besser435/Ted/VORON Print Files/Bunged Up Files (Made for v0.1)/Voron-0-0.1/DXF/Tophat/Side_v0.1_x2.DXF

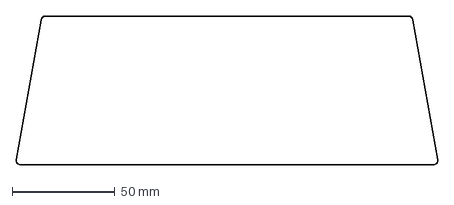
[picture p15: CAD file, 2023-02-20]
VORON Print Files/Bunged Up Files (Made for v0.1)/Voron-0-0.1/DXF/Tophat/Side_v0.1_x2.DXF
205.4 x 72.4 mm
