besser435/Ted/VORON Print Files/Bunged Up Files (Made for v0.1)/Voron-0-0.1/STLs/Panel_Mounting/Door_Latch_x2.STL

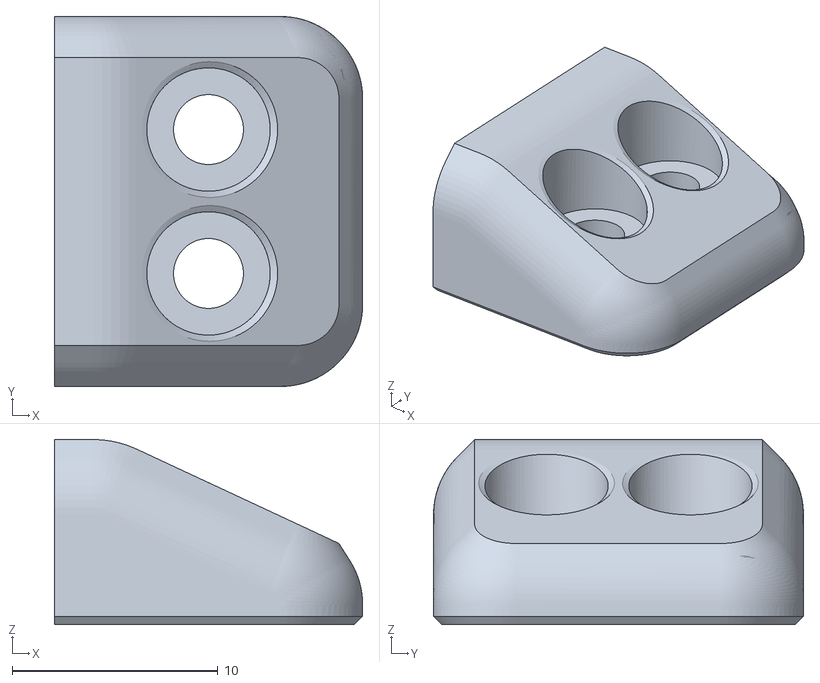
[picture p16: CAD file, 2023-02-20]
VORON Print Files/Bunged Up Files (Made for v0.1)/Voron-0-0.1/STLs/Panel_Mounting/Door_Latch_x2.STL
15.0 x 18.0 x 9.00
