besser435/Ted/VORON Print Files/Bunged Up Files (Made for v0.1)/Voron-0-0.1/STLs/Panel_Mounting/For_2mm_Panels/2mm_Bottom_Corner_Side_mirror_x1.STL

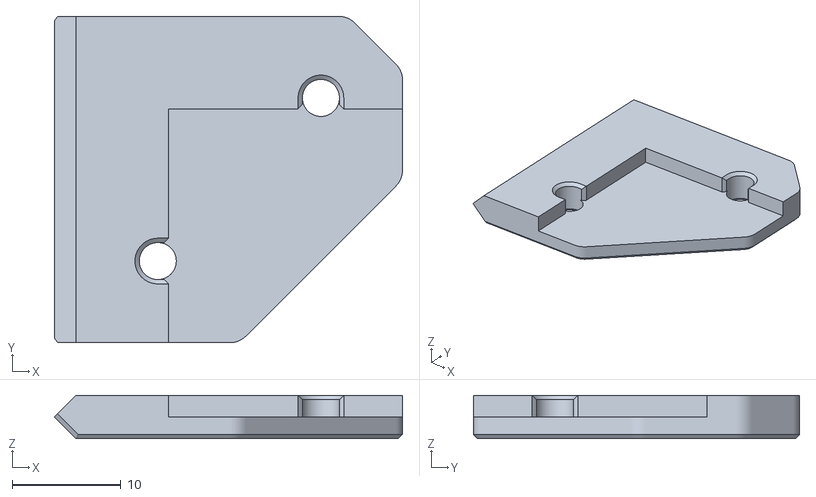
[picture p18: CAD file, 2023-02-20]
VORON Print Files/Bunged Up Files (Made for v0.1)/Voron-0-0.1/STLs/Panel_Mounting/For_2mm_Panels/2mm_Bottom_Corner_Side_mirror_x1.STL
32.0 x 30.0 x 4.00
