besser435/Ted/VORON Print Files/Bunged Up Files (Made for v0.1)/Voron-0-0.1/STLs/Toolheads/Bowden/[a]_Endstop_Strike_Block_x1.STL

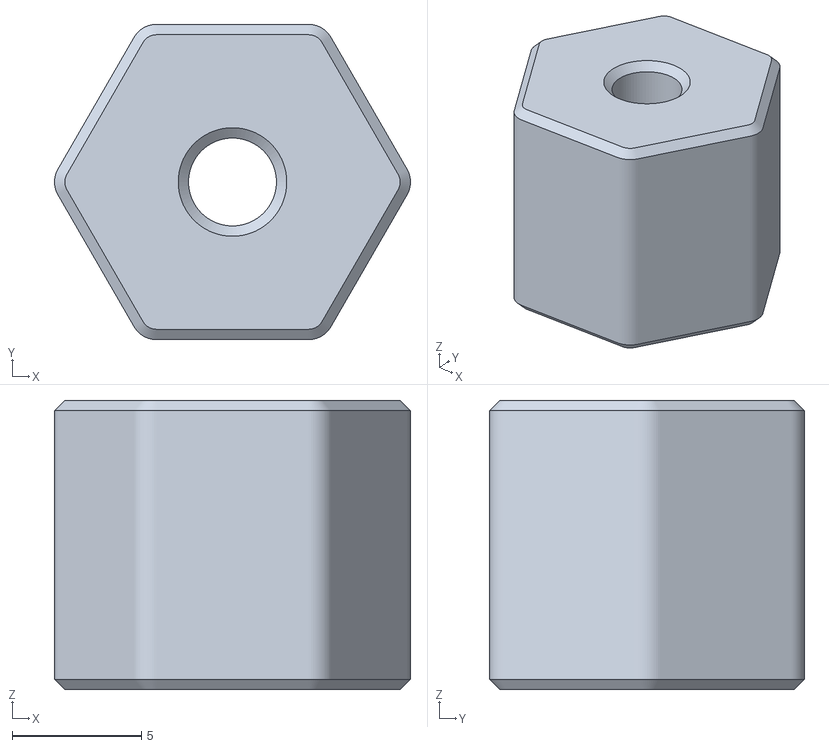
[picture p20: CAD file, 2023-02-20]
VORON Print Files/Bunged Up Files (Made for v0.1)/Voron-0-0.1/STLs/Toolheads/Bowden/[a]_Endstop_Strike_Block_x1.STL
13.8 x 12.2 x 11.2
