besser435/Ted/VORON Print Files/Bunged Up Files (Made for v0.1)/Voron-0-0.1/STLs/Toolheads/Bowden/Mosquito_Toolhead/Toolhead_Left_Mosquito_x1.STL

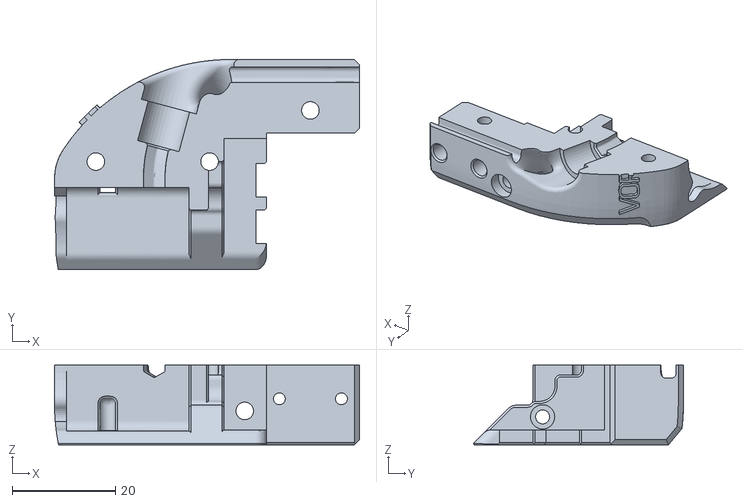
[picture p22: CAD file, 2023-02-20]
VORON Print Files/Bunged Up Files (Made for v0.1)/Voron-0-0.1/STLs/Toolheads/Bowden/Mosquito_Toolhead/Toolhead_Left_Mosquito_x1.STL
59.0 x 40.6 x 15.4
