besser435/Ted/VORON Print Files/Bunged Up Files (Made for v0.1)/Voron-0-0.1/STLs/Toolheads/Mini_Afterburner/Dragonfly_BMO_Toolhead_DD/[a]_Cowling_BMO_x1.STL

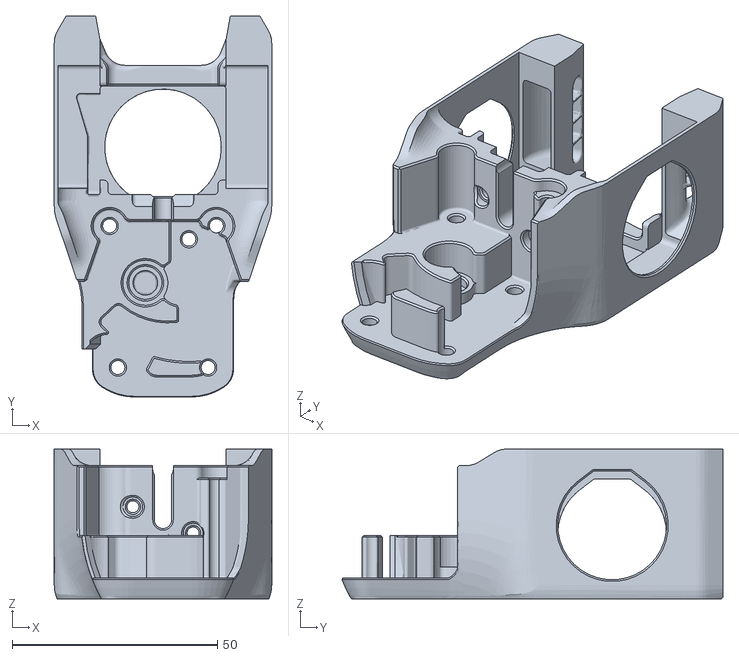
[picture p24: CAD file, 2023-02-20]
VORON Print Files/Bunged Up Files (Made for v0.1)/Voron-0-0.1/STLs/Toolheads/Mini_Afterburner/Dragonfly_BMO_Toolhead_DD/[a]_Cowling_BMO_x1.STL
53.0 x 92.8 x 36.5
