besser435/Ted/VORON Print Files/Bunged Up Files (Made for v0.1)/Voron-0-0.1/STLs/Toolheads/Mini_Afterburner/Motor_Frame_x1.stl

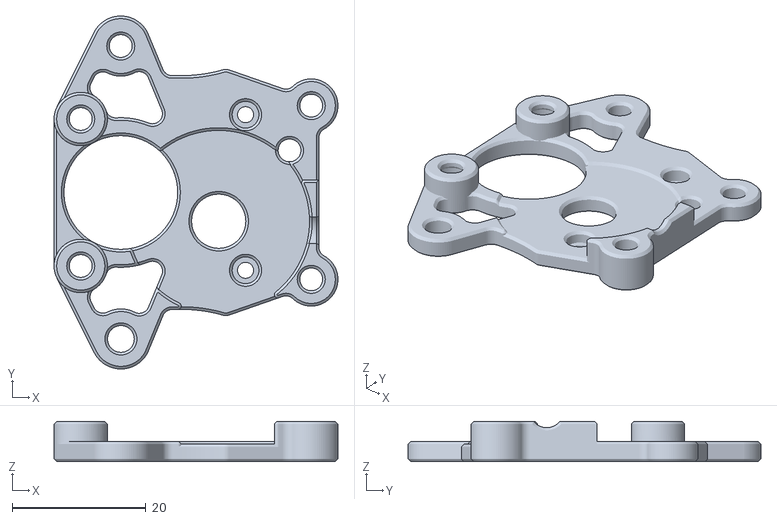
[picture p25: CAD file, 2023-02-20]
VORON Print Files/Bunged Up Files (Made for v0.1)/Voron-0-0.1/STLs/Toolheads/Mini_Afterburner/Motor_Frame_x1.stl
42.5 x 52.8 x 6.00
