besser435/Ted/VORON Print Files/Bunged Up Files (Made for v0.1)/Voron-0-0.1/STLs/Tophat/Left_and_Right_Midclip_x2.STL

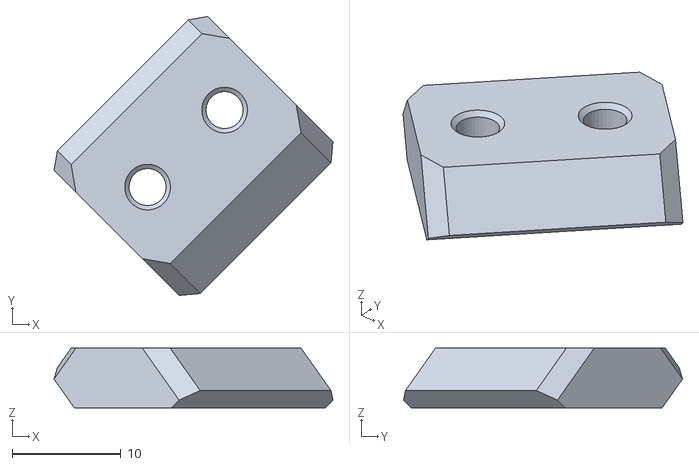
[picture p26: CAD file, 2023-02-20]
VORON Print Files/Bunged Up Files (Made for v0.1)/Voron-0-0.1/STLs/Tophat/Left_and_Right_Midclip_x2.STL
25.6 x 25.6 x 5.50
