besser435/Ted/VORON Print Files/Enclosure/Enclosure.3mf

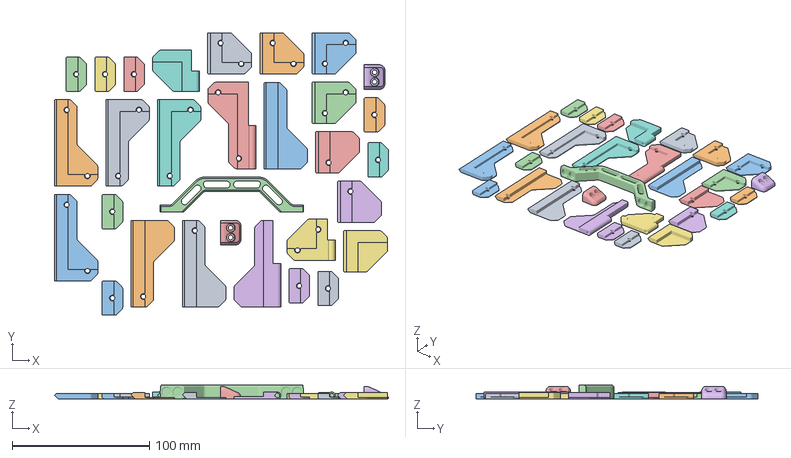
[picture p27: CAD file, 2023-02-20]
VORON Print Files/Enclosure/Enclosure.3mf
243.1 x 205.6 x 10.0 mm
2point5mm_Top_Corner_Rear_x1.STL
2point5mm_Top_Corner_Rear_mirror_x1.stl
2point5mm_Top_Corner_Front_x1.STL
2point5mm_Middle_Clip_x9.STL
2point5mm_Hinge_Top_B_x1.STL
2point5mm_Hinge_Top_A_x1.STL
2point5mm_Hinge_Bottom_B_x1.STL
2point5mm_Hinge_Bottom_A_x1.STL
2point5mm_Bottom_Corner_Side_x2.STL
2point5mm_Bottom_Corner_Side_mirror_x2.stl
2point5mm_Bottom_Corner_Rear_x1.STL
2point5mm_Bottom_Corner_Rear_mirror_x1.stl
2point5mm_Bottom_Corner_Front_x1.STL
2point5mm_Top_Corner_Side_x2.STL
2point5mm_Top_Corner_Side_mirror_x2.stl
Door_Handle_x1.STL
Door_Latch_x2.STL
