besser435/Ted/VORON Print Files/Enclosure/For_2.5mm_Panels/2point5mm_Top_Corner_Side_x2.STL

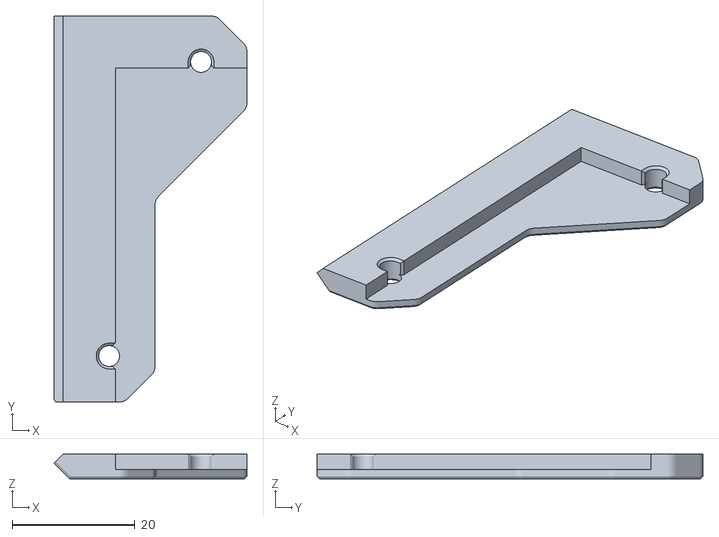
[picture p28: CAD file, 2023-02-20]
VORON Print Files/Enclosure/For_2.5mm_Panels/2point5mm_Top_Corner_Side_x2.STL
31.5 x 63.0 x 4.00
