besser435/Ted/VORON Print Files/Enclosure/For_2mm_Panels/2mm_Bottom_Corner_Rear_mirror_x1.STL

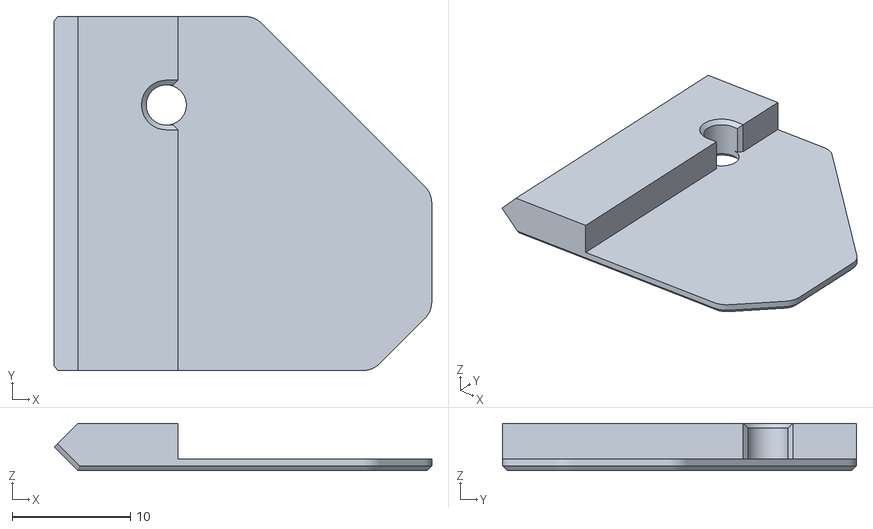
[picture p30: CAD file, 2023-02-20]
VORON Print Files/Enclosure/For_2mm_Panels/2mm_Bottom_Corner_Rear_mirror_x1.STL
32.0 x 30.0 x 4.00
