besser435/Ted/VORON Print Files/Enclosure/For_3mm_Panels/3mm_Top_Corner_Rear_x1.stl

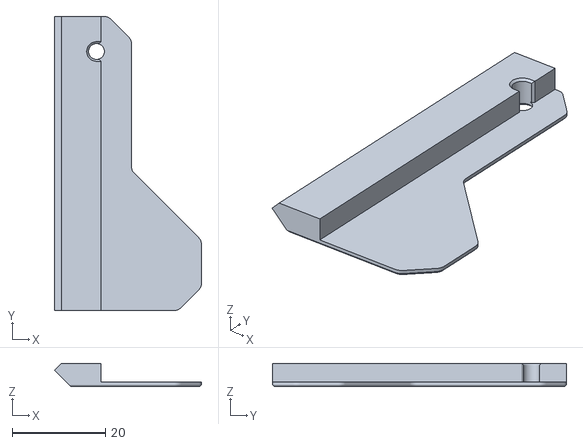
[picture p31: CAD file, 2023-02-20]
VORON Print Files/Enclosure/For_3mm_Panels/3mm_Top_Corner_Rear_x1.stl
31.5 x 63.0 x 5.00
