besser435/Ted/VORON Print Files/Main Parts/Batch 1 Main Parts/Accent Batch 1 Main Parts/[a]_Z_Endstop_Mount_x1.STL

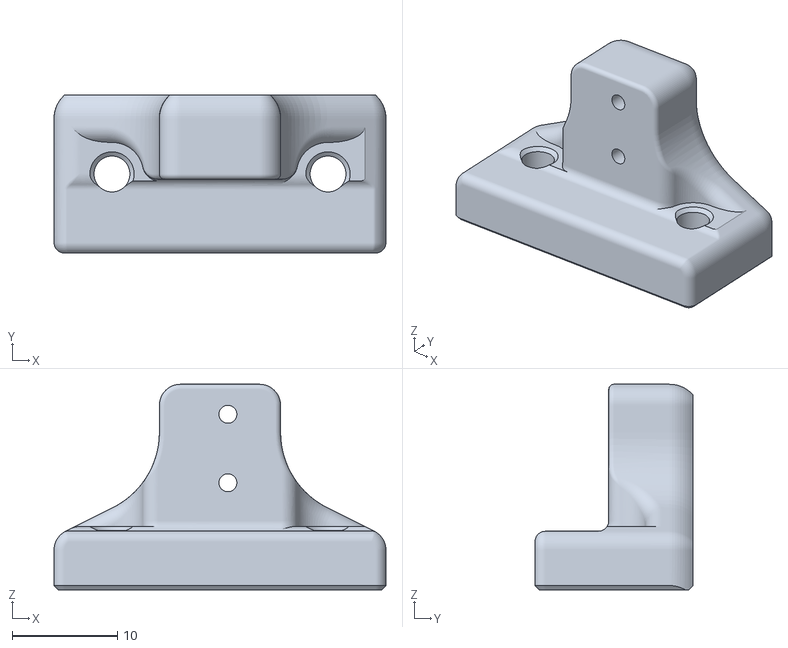
[picture p32: CAD file, 2023-02-20]
VORON Print Files/Main Parts/Batch 1 Main Parts/Accent Batch 1 Main Parts/[a]_Z_Endstop_Mount_x1.STL
31.5 x 15.0 x 19.5
