besser435/Ted/VORON Print Files/Main Parts/Batch 2 Main Parts/RPi_Frame_x1.stl

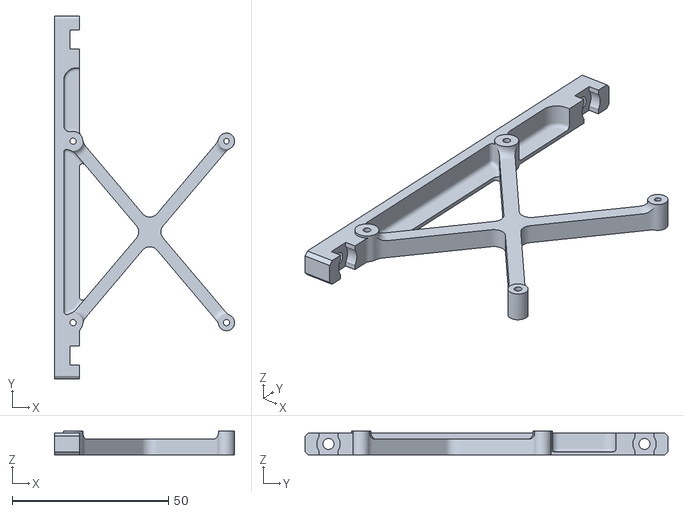
[picture p33: CAD file, 2023-02-20]
VORON Print Files/Main Parts/Batch 2 Main Parts/RPi_Frame_x1.stl
57.6 x 116.0 x 7.60
