besser435/Ted/VORON Print Files/Main Parts/Multiples Main Parts/One Part Skirts/V0_skirts_onepart.3mf

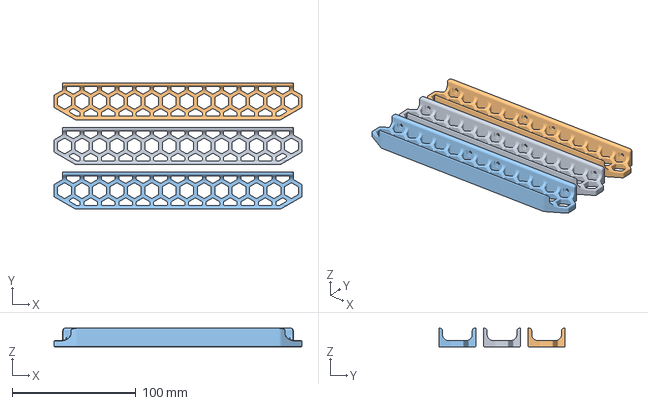
[picture p34: CAD file, 2023-02-20]
VORON Print Files/Main Parts/Multiples Main Parts/One Part Skirts/V0_skirts_onepart.3mf
200.0 x 102.0 x 15.0 mm
