besser435/Ted/VORON Print Files/Main Parts/Multiples Main Parts/Skirt_mirror_x3.STL

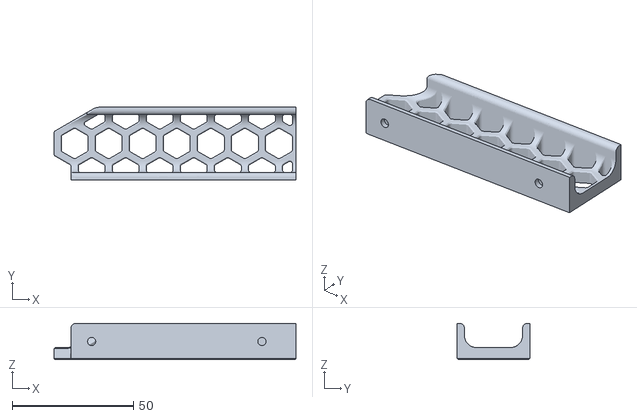
[picture p35: CAD file, 2023-02-20]
VORON Print Files/Main Parts/Multiples Main Parts/Skirt_mirror_x3.STL
100.0 x 30.0 x 15.0
