besser435/Ted/VORON Print Files/Main Parts/Nema17 Extruder latch and latch movey thing.3mf

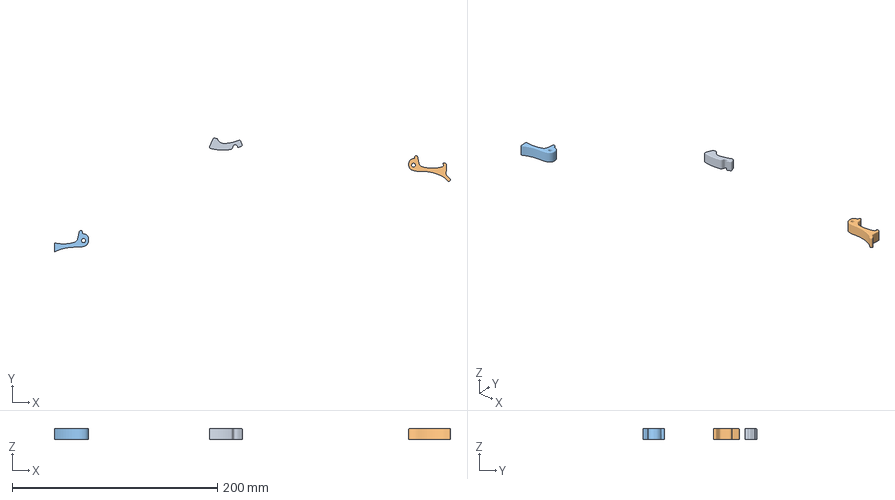
[picture p36: CAD file, 2023-02-20]
VORON Print Files/Main Parts/Nema17 Extruder latch and latch movey thing.3mf
385.8 x 110.9 x 11.1 mm
[a]_Latch_Shuttle_x1.STL
[a]_Latch_x1.STL
V0 Extruder Latch.stl
