besser435/Ted/VORON Print Files/New Cooling/Fan Shrouds, Embiggend Holes.3mf

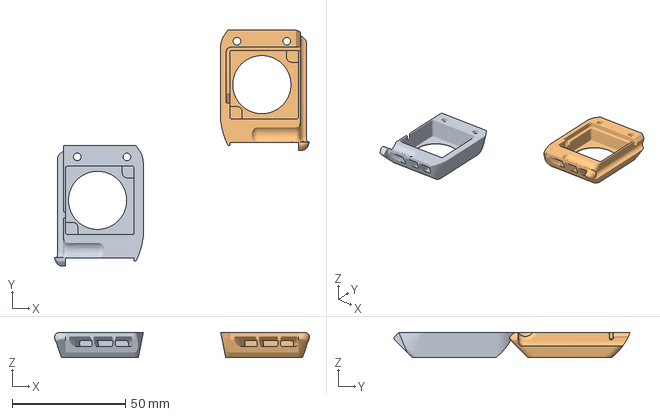
[picture p37: CAD file, 2023-02-20]
VORON Print Files/New Cooling/Fan Shrouds, Embiggend Holes.3mf
112.7 x 104.5 x 11.2 mm
VORON Part Cooling (6).stl_1
VORON Part Cooling (6).stl_2
