besser435/Ted/VORON Print Files/Toolhead/Accent Toolhead/[a]_Toolhead_Blower_Duct_Left_TV6_x1.STL

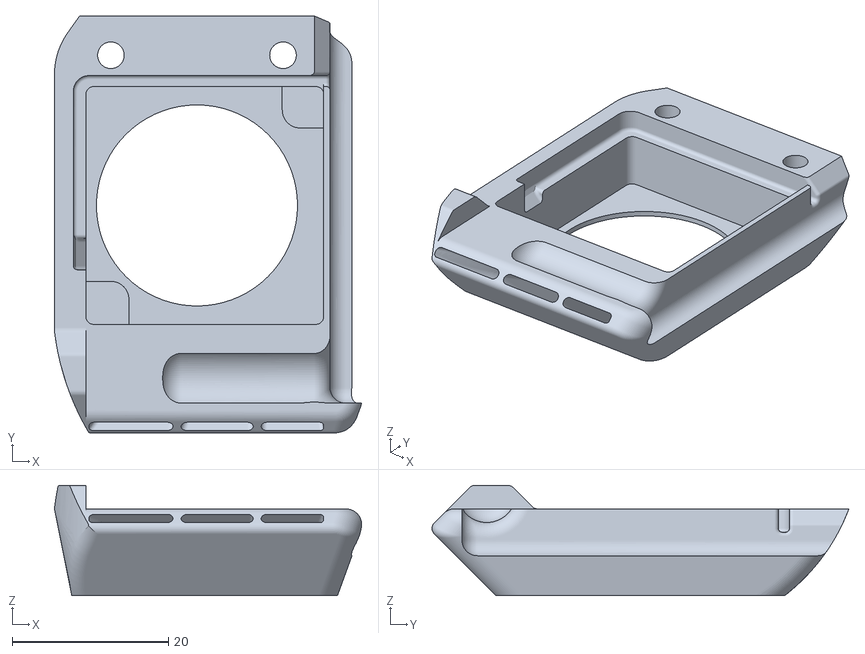
[picture p38: CAD file, 2023-02-20]
VORON Print Files/Toolhead/Accent Toolhead/[a]_Toolhead_Blower_Duct_Left_TV6_x1.STL
39.3 x 53.3 x 14.1
