besser435/Ted/VORON Print Files/Toolhead/Toolhead_Left_Threaded_V6_x1.STL

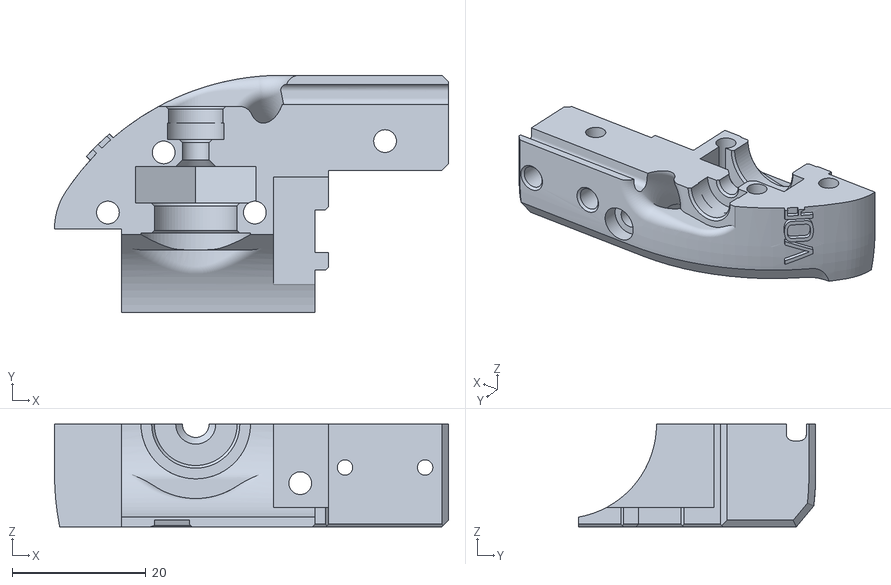
[picture p39: CAD file, 2023-02-20]
VORON Print Files/Toolhead/Toolhead_Left_Threaded_V6_x1.STL
59.0 x 35.6 x 15.4
