besser435/Ted/VORON Print Files/Tophat/TopHat_Left_x2.stl

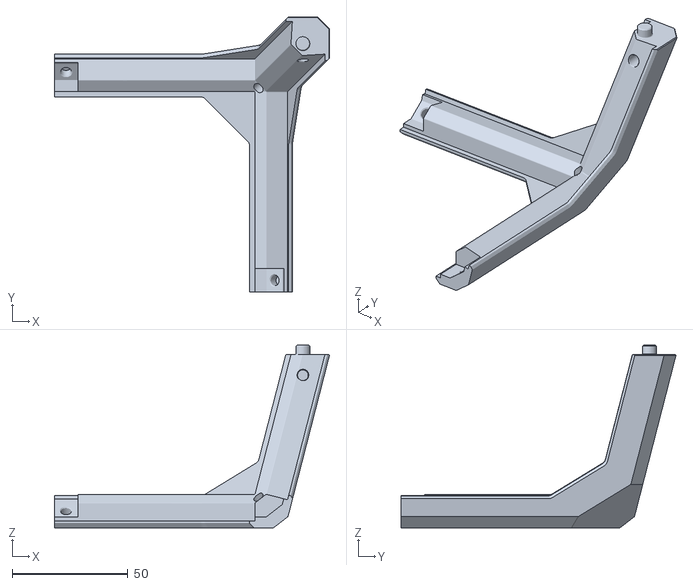
[picture p40: CAD file, 2023-02-20]
VORON Print Files/Tophat/TopHat_Left_x2.stl
119.0 x 119.0 x 79.0
