besser435/Ted/VORON Print Files/Tophat/TopHat_Panel_Mounting/For_2mm_Panels/2mm_TH_Mid_Clip_x4.STL

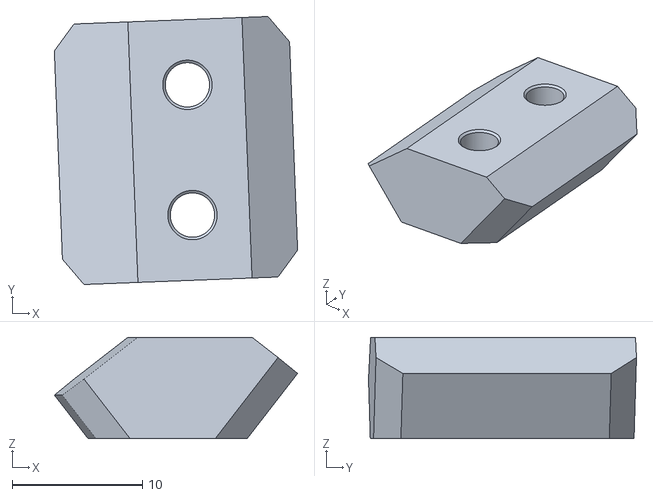
[picture p42: CAD file, 2023-02-20]
VORON Print Files/Tophat/TopHat_Panel_Mounting/For_2mm_Panels/2mm_TH_Mid_Clip_x4.STL
18.7 x 20.6 x 7.78
