besser435/Ted/VORON Print Files/Tophat/TopHat_Panel_Mounting/For_3mm_Panels/3mm_TH_Top_Corner_Clips_x4.STL

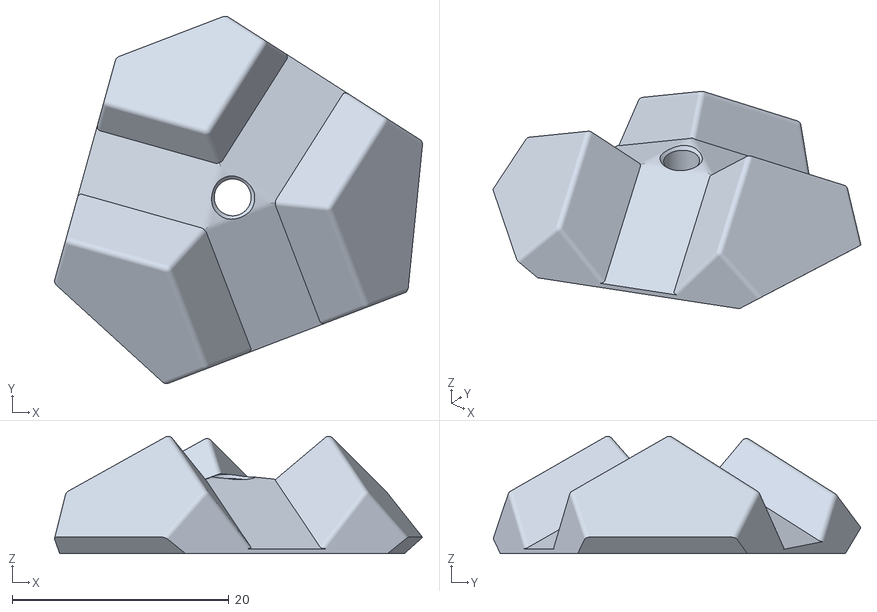
[picture p43: CAD file, 2023-02-20]
VORON Print Files/Tophat/TopHat_Panel_Mounting/For_3mm_Panels/3mm_TH_Top_Corner_Clips_x4.STL
34.0 x 33.9 x 10.8
