besser435/Ted/VORON Print Files/VORON-0 Everything/DXFs/Deck_Panel_Rear_V0.DXF

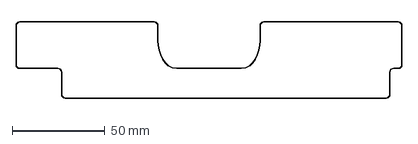
[picture p44: CAD file, 2023-02-20]
VORON Print Files/VORON-0 Everything/DXFs/Deck_Panel_Rear_V0.DXF
208.0 x 41.0 mm
