besser435/Ted/VORON Print Files/VORON-0 Everything/STLs/[a]_Foot_Front_x2.stl

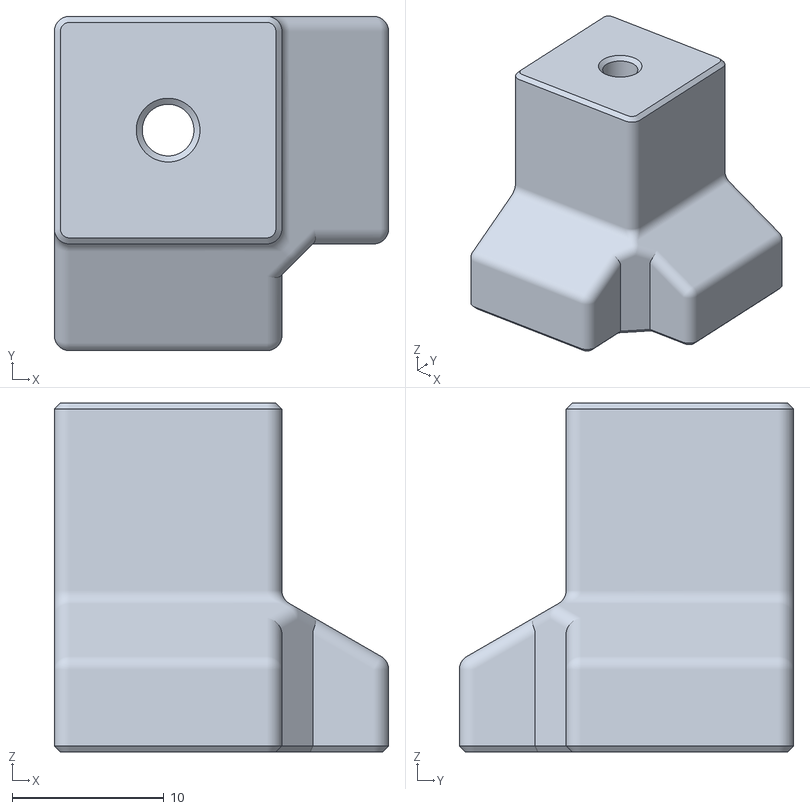
[picture p45: CAD file, 2023-02-20]
VORON Print Files/VORON-0 Everything/STLs/[a]_Foot_Front_x2.stl
22.0 x 22.0 x 23.0
