besser435/Ted/VORON Print Files/VORON-0 Everything/STLs/Mosquito_Toolhead/Toolhead_Right_Mosquito_x1.STL

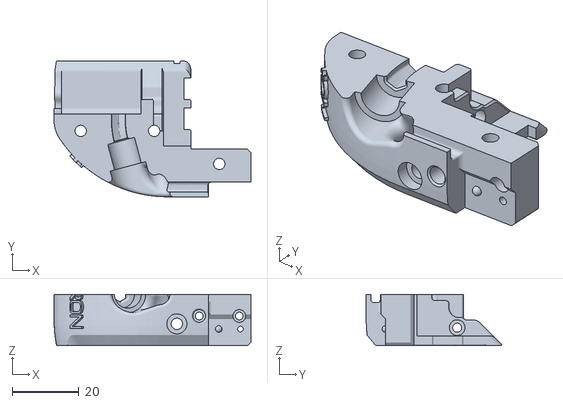
[picture p46: CAD file, 2023-02-20]
VORON Print Files/VORON-0 Everything/STLs/Mosquito_Toolhead/Toolhead_Right_Mosquito_x1.STL
59.0 x 40.6 x 15.4
