besser435/Ted/VORON Print Files/VORON-0 Everything/STLs/V0_TopHat/TopHat_Panel_Mounting/For_2.5mm_Panels/2point5mm_TH_Mid_Clip_x4.STL

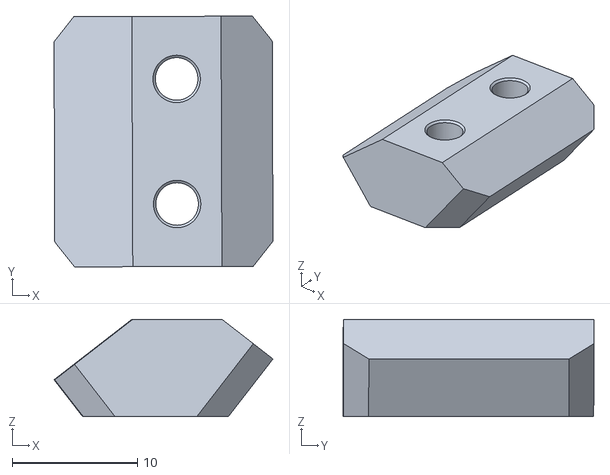
[picture p47: CAD file, 2023-02-20]
VORON Print Files/VORON-0 Everything/STLs/V0_TopHat/TopHat_Panel_Mounting/For_2.5mm_Panels/2point5mm_TH_Mid_Clip_x4.STL
17.5 x 20.1 x 7.78
