besser435/Ted/VORON Print Files/VORON-0 Everything/STLs/V0_TopHat/TopHat_Panel_Mounting/For_2mm_Panels/2mm_TH_Top_Corner_Clips_x4.STL

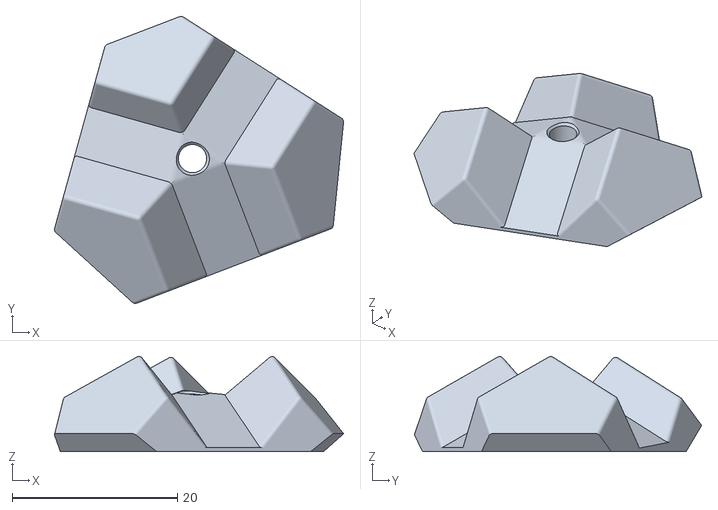
[picture p48: CAD file, 2023-02-20]
VORON Print Files/VORON-0 Everything/STLs/V0_TopHat/TopHat_Panel_Mounting/For_2mm_Panels/2mm_TH_Top_Corner_Clips_x4.STL
34.9 x 34.7 x 11.5
