besser435/Ted/VORON Print Files/VORON-0 Everything/STLs/V0_TopHat/Unibody_Tophat/Unibody_Tophat_x1.STL

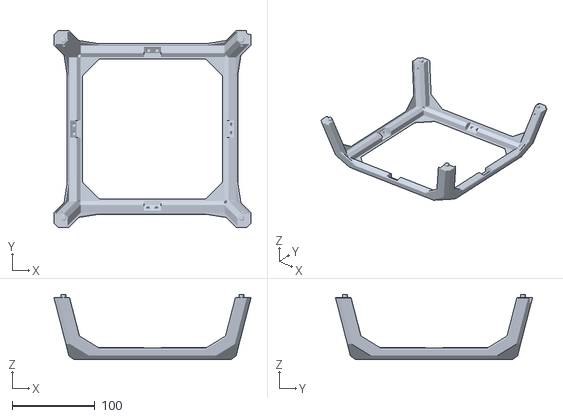
[picture p49: CAD file, 2023-02-20]
VORON Print Files/VORON-0 Everything/STLs/V0_TopHat/Unibody_Tophat/Unibody_Tophat_x1.STL
238.1 x 238.1 x 79.0
