besser435/Ted/VORON Print Files/Bunged Up Files (Made for v0.1)/Enclosure (Contains Multiples)/Lower_Corner_1_and_3_Clip_x2.stl

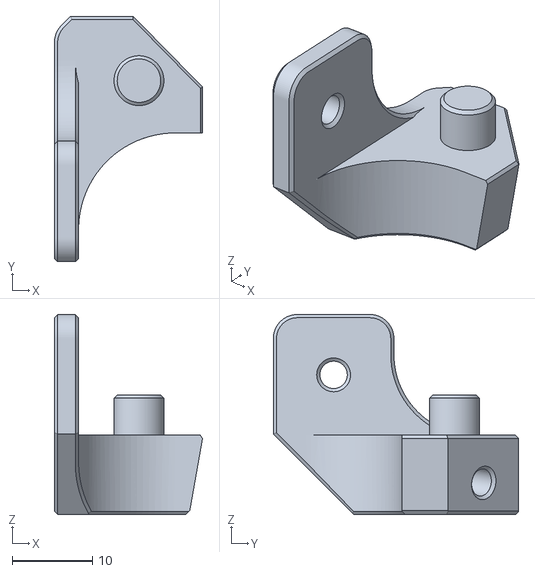
[picture p50: CAD file, 2023-02-20]
VORON Print Files/Bunged Up Files (Made for v0.1)/Enclosure (Contains Multiples)/Lower_Corner_1_and_3_Clip_x2.stl
18.4 x 30.5 x 24.8
