besser435/Ted/VORON Print Files/Bunged Up Files (Made for v0.1)/Mulitples of parts/Skirt_x3.STL

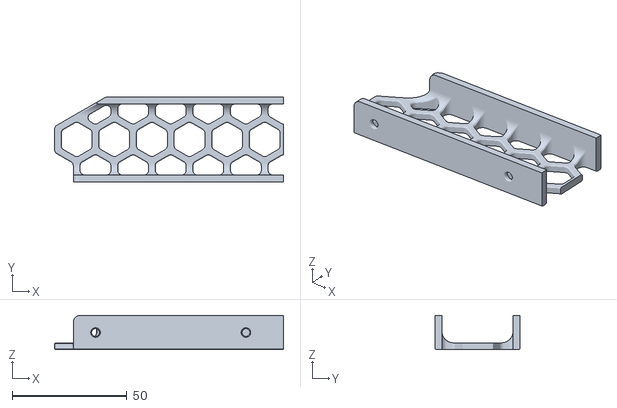
[picture p51: CAD file, 2023-02-20]
VORON Print Files/Bunged Up Files (Made for v0.1)/Mulitples of parts/Skirt_x3.STL
100.0 x 37.0 x 15.0
