besser435/Ted/VORON Print Files/Bunged Up Files (Made for v0.1)/Regular Parts/Batch 1/Accent/A_Drive_Frame_Lower_x1.stl

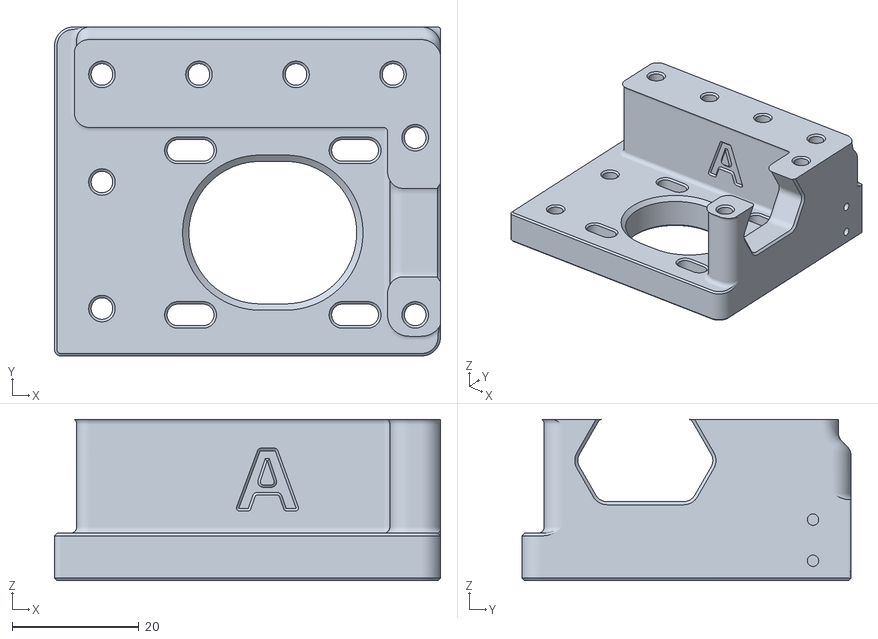
[picture p52: CAD file, 2023-02-20]
VORON Print Files/Bunged Up Files (Made for v0.1)/Regular Parts/Batch 1/Accent/A_Drive_Frame_Lower_x1.stl
61.0 x 52.0 x 25.5
