besser435/Ted/VORON Print Files/Bunged Up Files (Made for v0.1)/Regular Parts/Batch 2 (B)/PSU_Cover_x1.STL

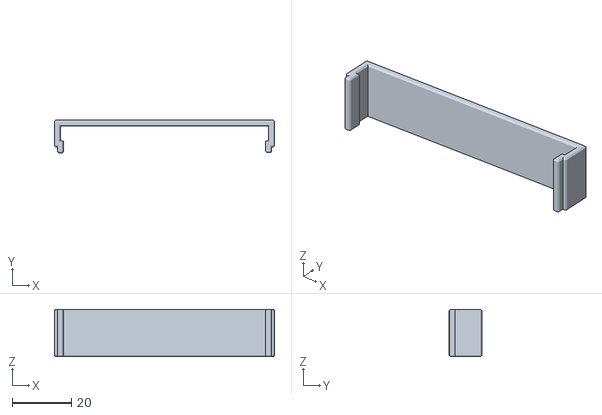
[picture p54: CAD file, 2023-02-20]
VORON Print Files/Bunged Up Files (Made for v0.1)/Regular Parts/Batch 2 (B)/PSU_Cover_x1.STL
74.2 x 11.0 x 16.0
