besser435/Ted/VORON Print Files/Bunged Up Files (Made for v0.1)/Voron-0-0.1/DXF/Rear_Panel_x1.DXF

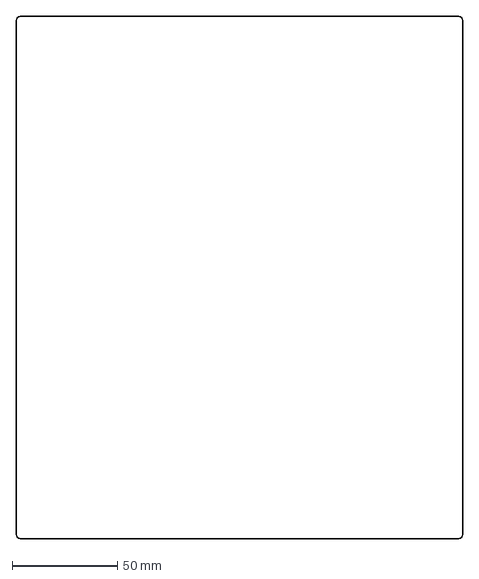
[picture p55: CAD file, 2023-02-20]
VORON Print Files/Bunged Up Files (Made for v0.1)/Voron-0-0.1/DXF/Rear_Panel_x1.DXF
212.0 x 248.0 mm
