besser435/Ted/VORON Print Files/Bunged Up Files (Made for v0.1)/Voron-0-0.1/DXF/Tophat/Front_Rear_v0.1_x2.DXF

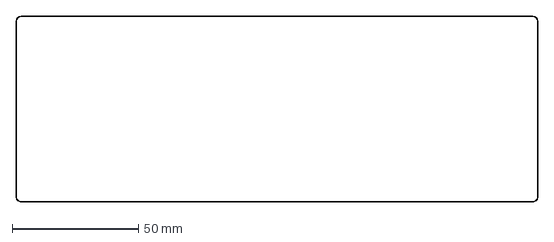
[picture p56: CAD file, 2023-02-20]
VORON Print Files/Bunged Up Files (Made for v0.1)/Voron-0-0.1/DXF/Tophat/Front_Rear_v0.1_x2.DXF
206.5 x 73.4 mm
