besser435/Ted/VORON Print Files/Bunged Up Files (Made for v0.1)/Voron-0-0.1/STLs/Panel_Mounting/Door_Handle_x1.STL

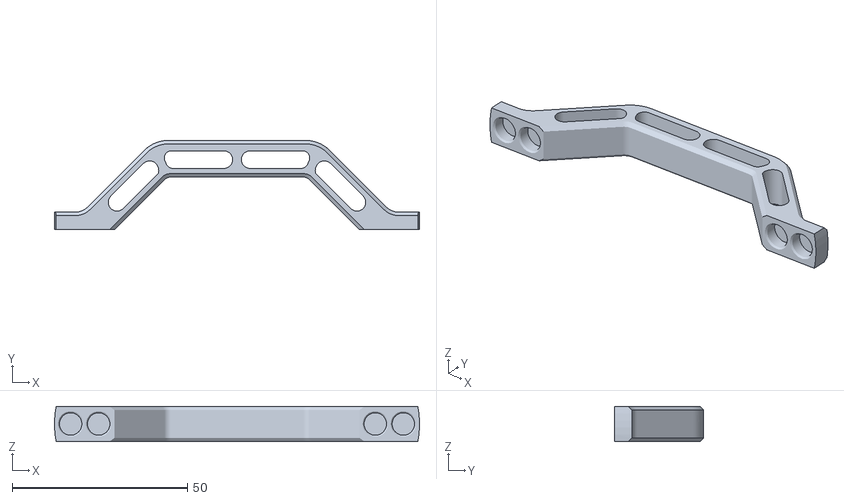
[picture p57: CAD file, 2023-02-20]
VORON Print Files/Bunged Up Files (Made for v0.1)/Voron-0-0.1/STLs/Panel_Mounting/Door_Handle_x1.STL
104.2 x 25.5 x 10.0
