besser435/Ted/VORON Print Files/Bunged Up Files (Made for v0.1)/Voron-0-0.1/STLs/Panel_Mounting/For_2.5mm_Panels/2point5mm_Hinge_Bottom_A_x1.STL

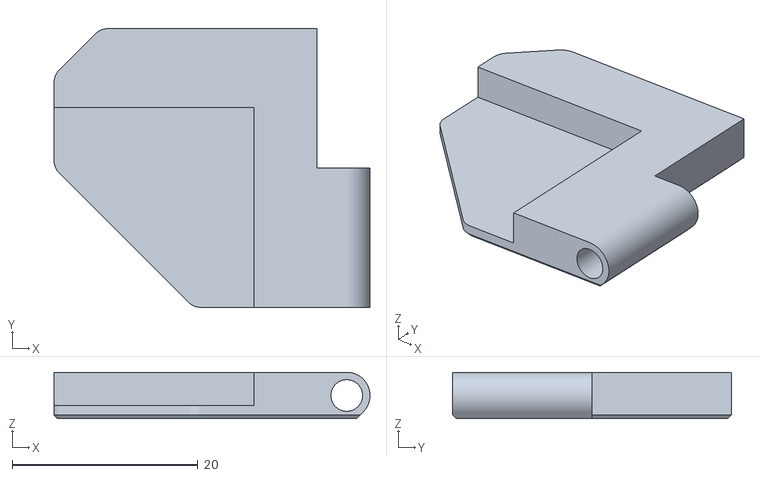
[picture p58: CAD file, 2023-02-20]
VORON Print Files/Bunged Up Files (Made for v0.1)/Voron-0-0.1/STLs/Panel_Mounting/For_2.5mm_Panels/2point5mm_Hinge_Bottom_A_x1.STL
34.0 x 30.0 x 5.00
