besser435/Ted/VORON Print Files/Bunged Up Files (Made for v0.1)/Voron-0-0.1/STLs/Panel_Mounting/For_3mm_Panels/3mm_Bottom_Corner_Front_x1.stl

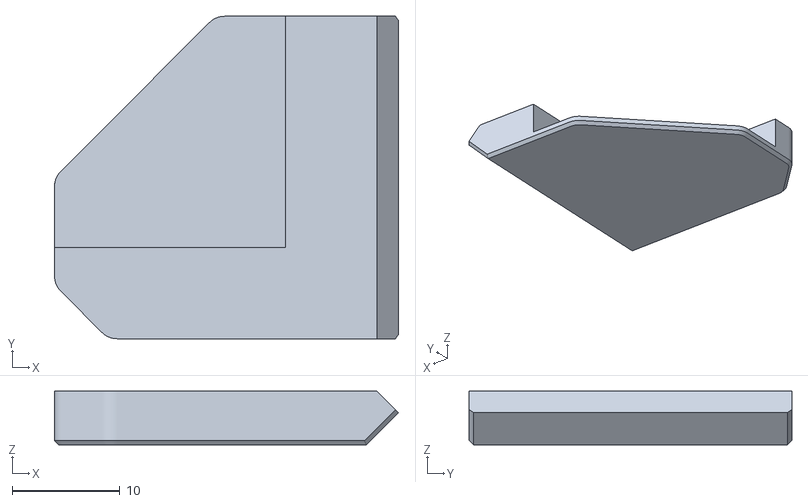
[picture p59: CAD file, 2023-02-20]
VORON Print Files/Bunged Up Files (Made for v0.1)/Voron-0-0.1/STLs/Panel_Mounting/For_3mm_Panels/3mm_Bottom_Corner_Front_x1.stl
32.0 x 30.0 x 5.00
