besser435/Ted/VORON Print Files/Bunged Up Files (Made for v0.1)/Voron-0-0.1/STLs/Toolheads/Mini_Afterburner/Latch_DD_x1.stl

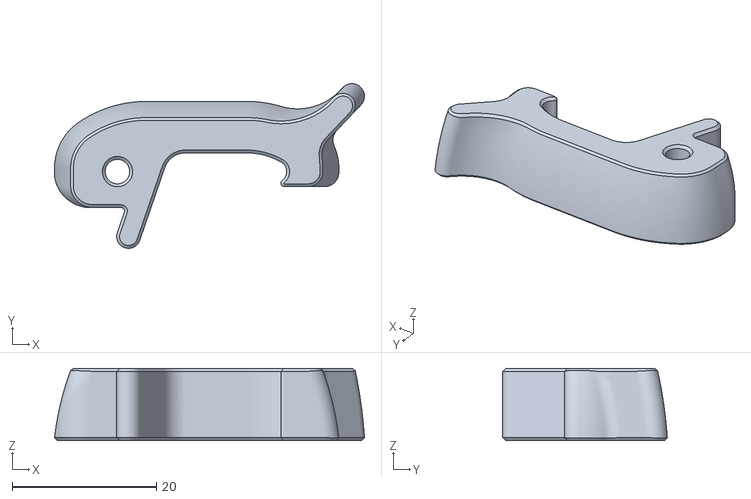
[picture p60: CAD file, 2023-02-20]
VORON Print Files/Bunged Up Files (Made for v0.1)/Voron-0-0.1/STLs/Toolheads/Mini_Afterburner/Latch_DD_x1.stl
43.0 x 22.9 x 10.0
