besser435/Ted/VORON Print Files/Bunged Up Files (Made for v0.1)/Voron-0-0.1/STLs/Tools/V0_Extrusion_Drilling_Guide_x1.STL

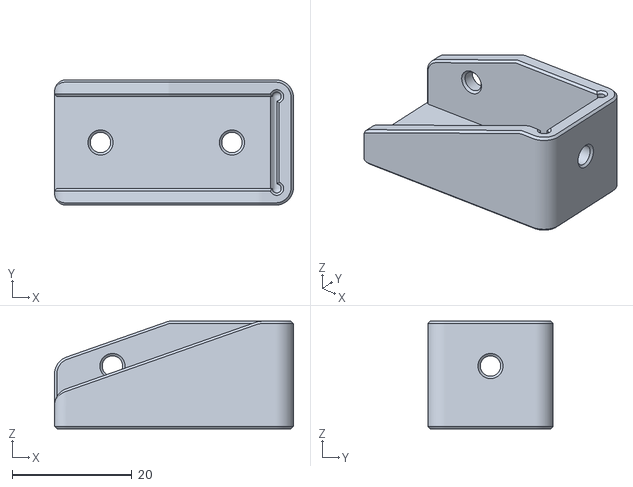
[picture p61: CAD file, 2023-02-20]
VORON Print Files/Bunged Up Files (Made for v0.1)/Voron-0-0.1/STLs/Tools/V0_Extrusion_Drilling_Guide_x1.STL
40.0 x 21.0 x 18.0
