besser435/Ted/VORON Print Files/Bunged Up Files (Made for v0.1)/Voron-0-0.1/STLs/Tophat/Tophat_Part2_x2.STL

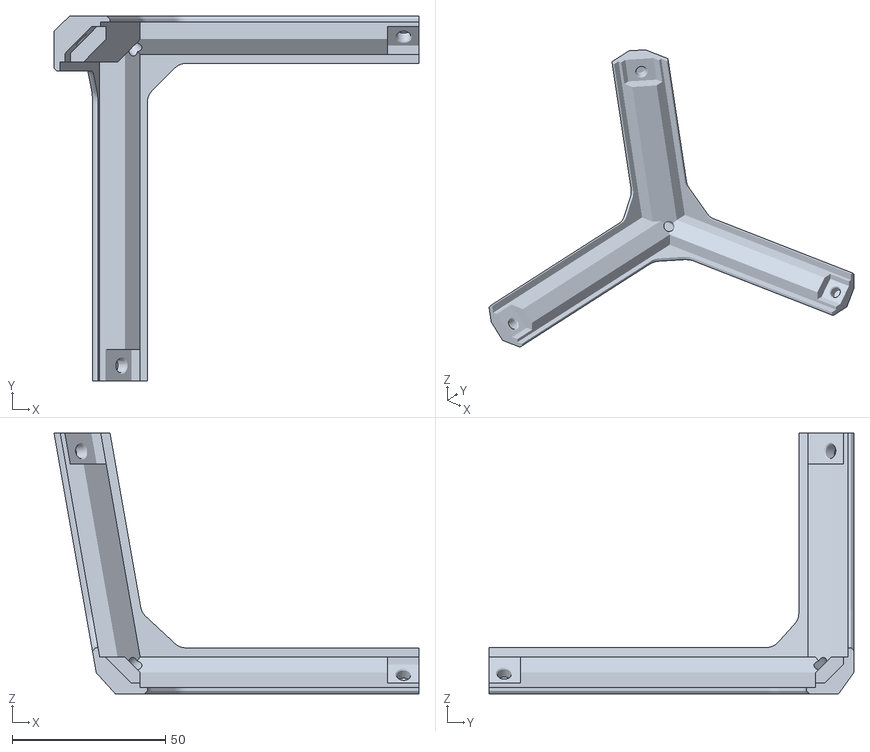
[picture p62: CAD file, 2023-02-20]
VORON Print Files/Bunged Up Files (Made for v0.1)/Voron-0-0.1/STLs/Tophat/Tophat_Part2_x2.STL
119.0 x 119.0 x 85.0
