besser435/Ted/VORON Print Files/Enclosure/For_2.5mm_Panels/Single Frame Door/2point5mm_Bottom_Corner_Front_x1.STL

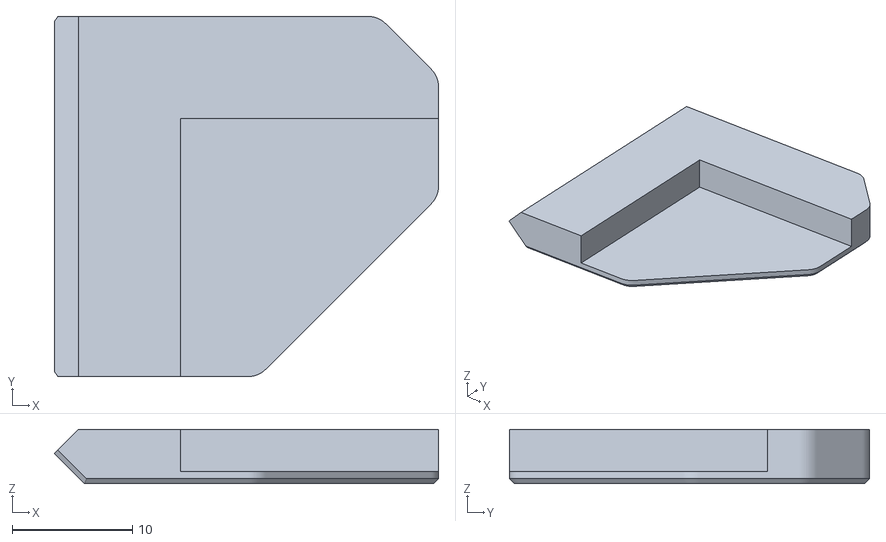
[picture p63: CAD file, 2023-02-20]
VORON Print Files/Enclosure/For_2.5mm_Panels/Single Frame Door/2point5mm_Bottom_Corner_Front_x1.STL
32.0 x 30.0 x 4.50
