besser435/Ted/VORON Print Files/Enclosure/For_2mm_Panels/2mm_Top_Corner_Rear_x1.STL

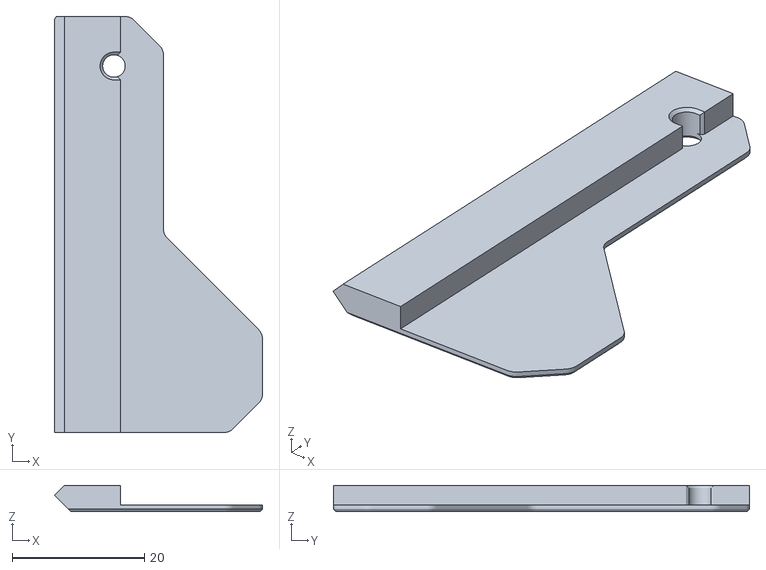
[picture p64: CAD file, 2023-02-20]
VORON Print Files/Enclosure/For_2mm_Panels/2mm_Top_Corner_Rear_x1.STL
31.5 x 63.0 x 4.00
