besser435/Ted/VORON Print Files/Enclosure/For_3mm_Panels/3mm_Middle_Clip_x9.stl

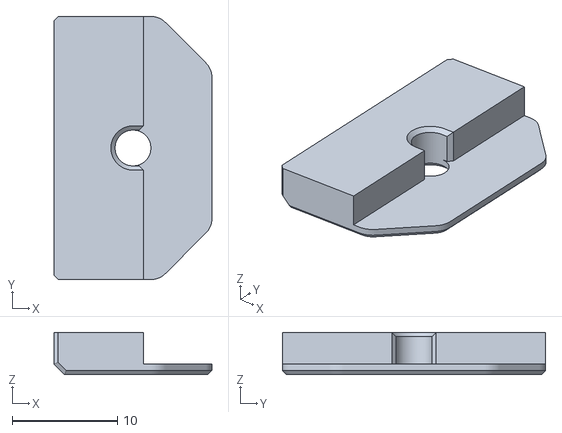
[picture p65: CAD file, 2023-02-20]
VORON Print Files/Enclosure/For_3mm_Panels/3mm_Middle_Clip_x9.stl
15.0 x 25.0 x 4.00
