besser435/Ted/VORON Print Files/Main Parts/Batch 1 Main Parts/Accent Batch 1 Main Parts/A_Drive_Frame_Top_x1.STL

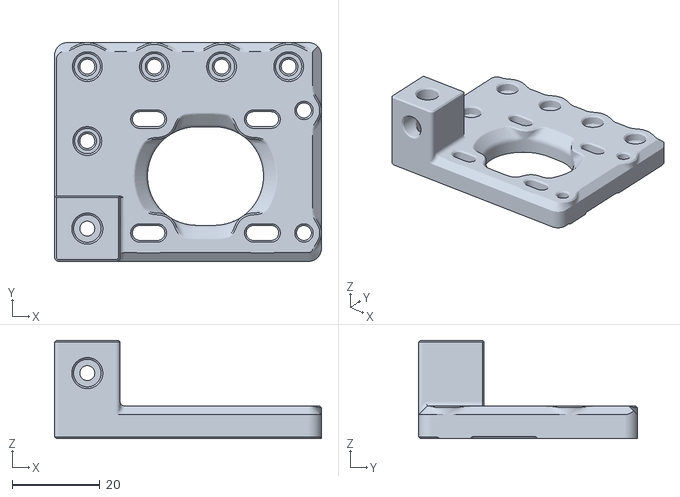
[picture p66: CAD file, 2023-02-20]
VORON Print Files/Main Parts/Batch 1 Main Parts/Accent Batch 1 Main Parts/A_Drive_Frame_Top_x1.STL
61.0 x 50.0 x 22.5
