besser435/Ted/VORON Print Files/Main Parts/Batch 1 Main Parts/MGN7_Rail_Guide_x2.STL

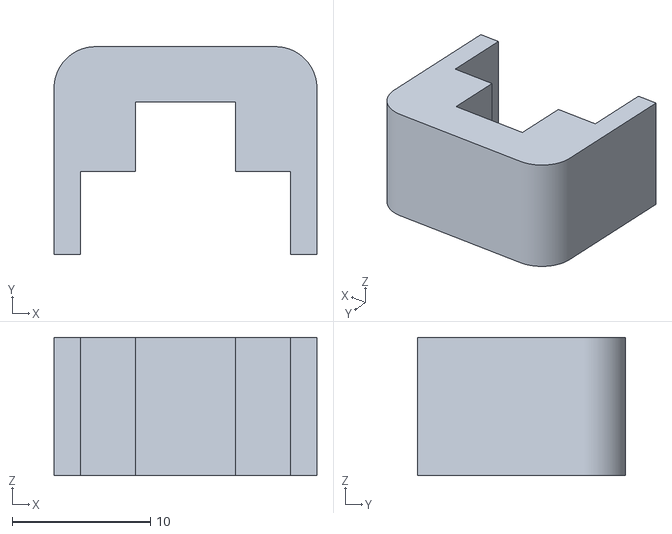
[picture p67: CAD file, 2023-02-20]
VORON Print Files/Main Parts/Batch 1 Main Parts/MGN7_Rail_Guide_x2.STL
19.0 x 15.0 x 10.0
