besser435/Ted/VORON Print Files/Main Parts/Batch 2 Main Parts/Spool_Holder_V0_x1.STL

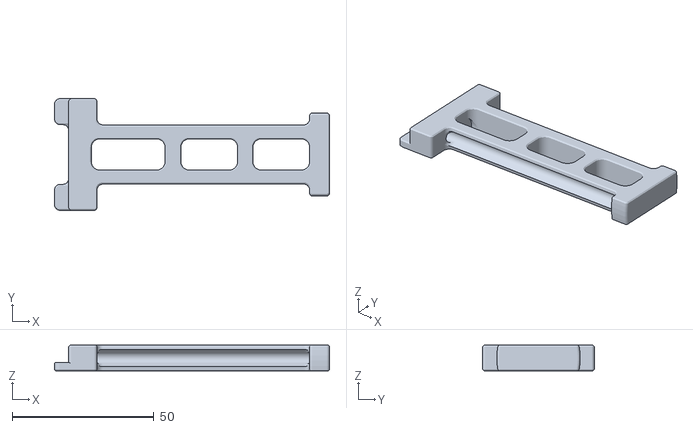
[picture p68: CAD file, 2023-02-20]
VORON Print Files/Main Parts/Batch 2 Main Parts/Spool_Holder_V0_x1.STL
97.0 x 39.4 x 9.00
