besser435/Ted/VORON Print Files/Main Parts/Extruder.3mf

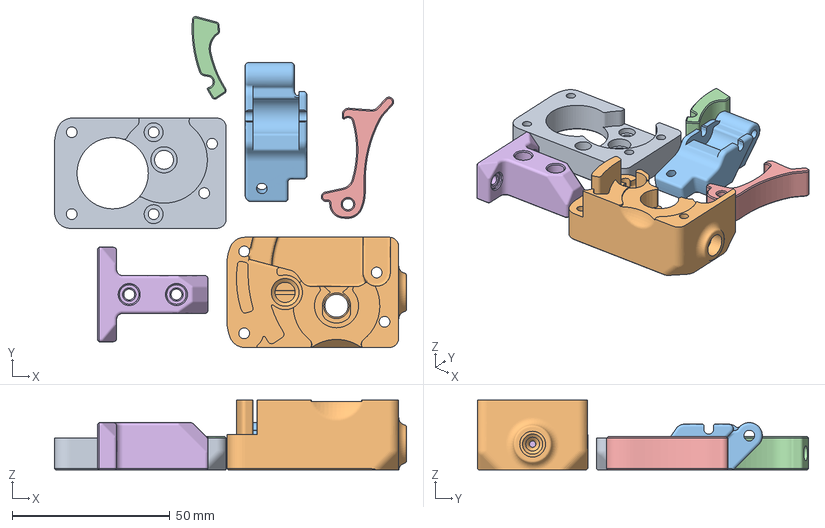
[picture p69: CAD file, 2023-02-20]
VORON Print Files/Main Parts/Extruder.3mf
111.8 x 105.1 x 22.2 mm
Motor_Frame_x1.STL
Pocketwatch_Guts_x1.STL
[a]_Guidler_Door_x1.STL
[a]_Latch_Shuttle_x1.STL
[a]_Latch_x1.STL
[a]_Mount_Bracket_x1.STL
