besser435/Ted/VORON Print Files/Main Parts/Multiples Main Parts/Multiple Accent Parts/[a]_Foot_Rear_x2.STL

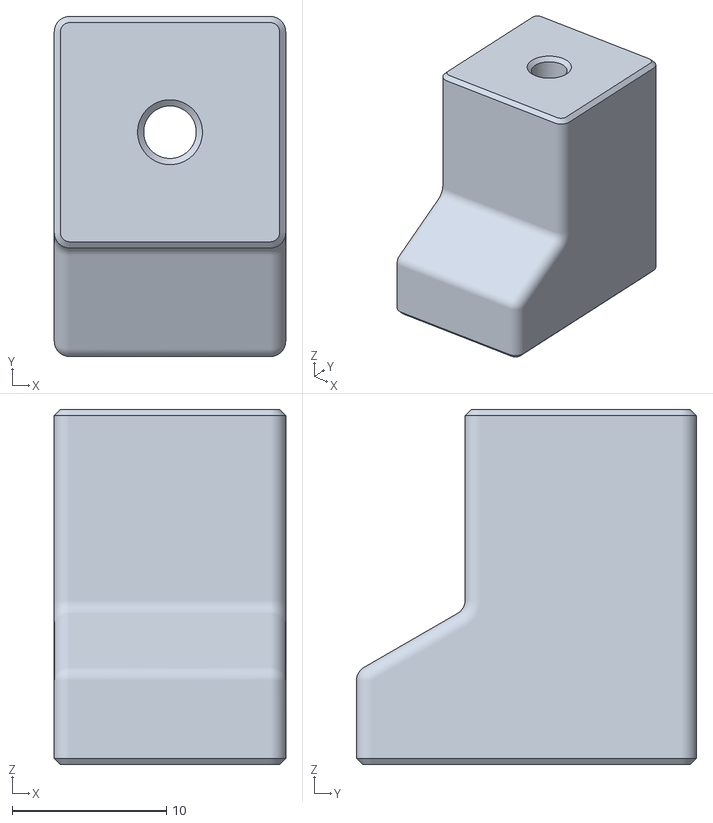
[picture p70: CAD file, 2023-02-20]
VORON Print Files/Main Parts/Multiples Main Parts/Multiple Accent Parts/[a]_Foot_Rear_x2.STL
15.0 x 22.0 x 23.0
