besser435/Ted/VORON Print Files/Tophat/TopHat_Panel_Mounting/For_2mm_Panels/2mm_TH_Lower_Corner_Clip_Left_x2.STL

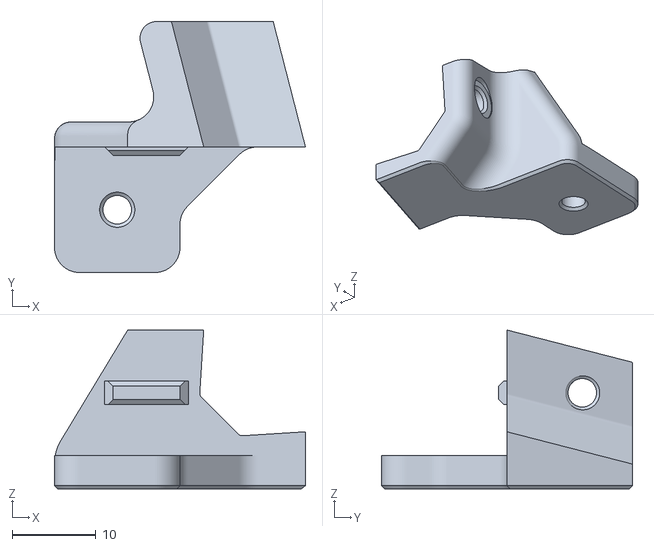
[picture p72: CAD file, 2023-02-20]
VORON Print Files/Tophat/TopHat_Panel_Mounting/For_2mm_Panels/2mm_TH_Lower_Corner_Clip_Left_x2.STL
30.0 x 30.0 x 19.0
