besser435/Ted/VORON Print Files/Tophat/TopHat_Panel_Mounting/For_3mm_Panels/3mm_TH_Lower_Corner_Clip_Right_x2.stl

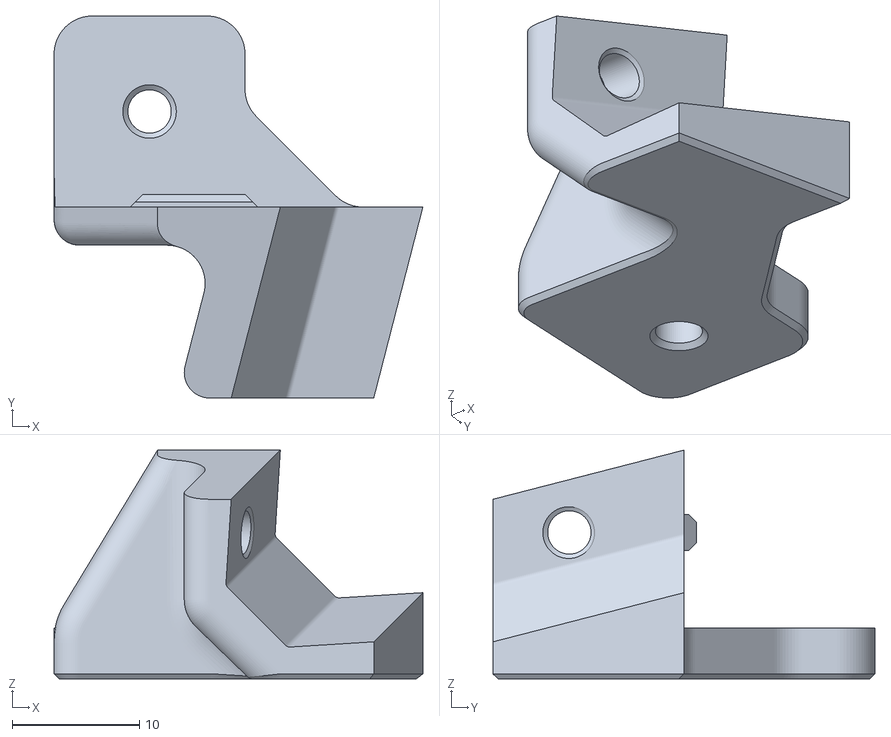
[picture p73: CAD file, 2023-02-20]
VORON Print Files/Tophat/TopHat_Panel_Mounting/For_3mm_Panels/3mm_TH_Lower_Corner_Clip_Right_x2.stl
29.0 x 30.0 x 18.0
