besser435/Ted/VORON Print Files/VORON-0 Everything/DXFs/TopHat_Side_Panel.DXF

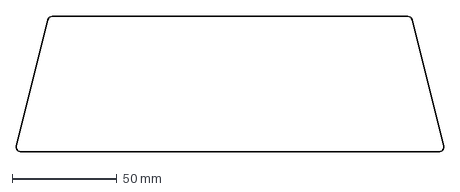
[picture p74: CAD file, 2023-02-20]
VORON Print Files/VORON-0 Everything/DXFs/TopHat_Side_Panel.DXF
204.0 x 64.4 mm
