besser435/Ted/VORON Print Files/VORON-0 Everything/STLs/V0_Panel_Mounting/For_2.5mm_Panels/2point5mm_Bottom_Corner_Rear_x1.STL

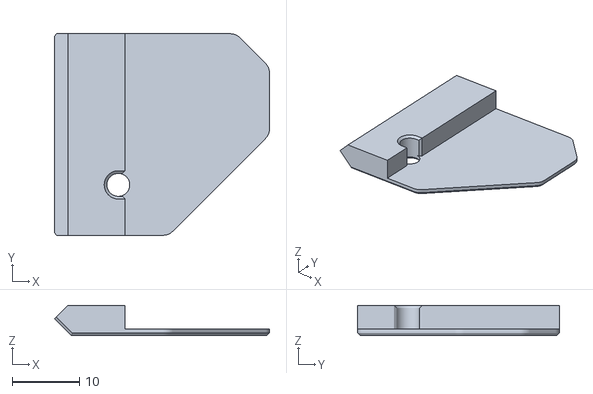
[picture p75: CAD file, 2023-02-20]
VORON Print Files/VORON-0 Everything/STLs/V0_Panel_Mounting/For_2.5mm_Panels/2point5mm_Bottom_Corner_Rear_x1.STL
32.0 x 30.0 x 4.50
