besser435/Ted/VORON Print Files/Bunged Up Files (Made for v0.1)/Enclosure (Contains Multiples)/Front_and_Rear_Midclip_x2.STL

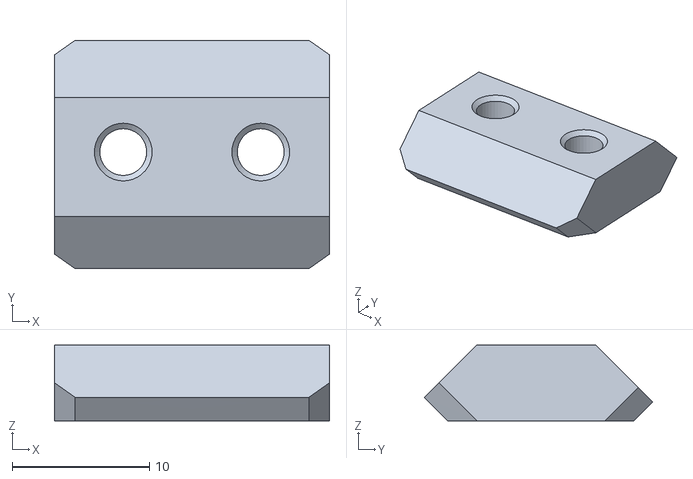
[picture p76: CAD file, 2023-02-20]
VORON Print Files/Bunged Up Files (Made for v0.1)/Enclosure (Contains Multiples)/Front_and_Rear_Midclip_x2.STL
20.0 x 16.6 x 5.50
