besser435/Ted/VORON Print Files/Bunged Up Files (Made for v0.1)/Regular Parts/Batch 1/Accent/A_Idler_Lower_x1.stl

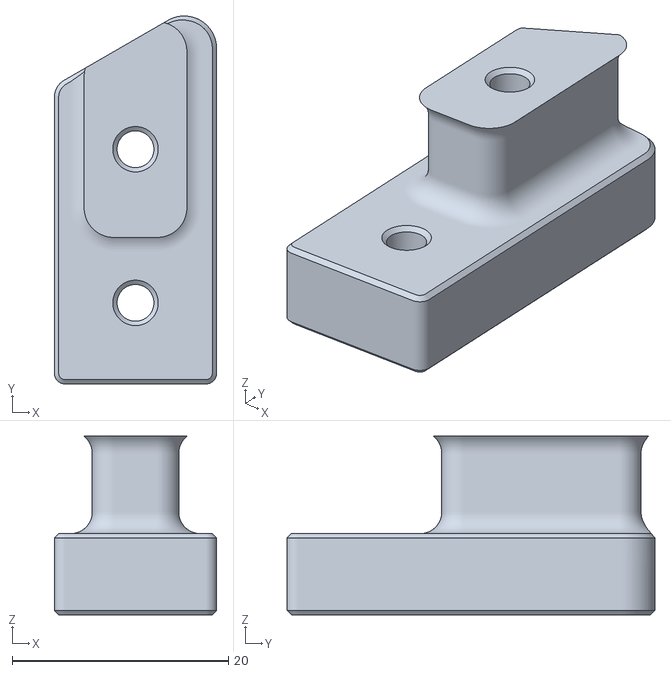
[picture p77: CAD file, 2023-02-20]
VORON Print Files/Bunged Up Files (Made for v0.1)/Regular Parts/Batch 1/Accent/A_Idler_Lower_x1.stl
15.0 x 34.0 x 16.5
