besser435/Ted/VORON Print Files/Bunged Up Files (Made for v0.1)/Regular Parts/Batch 1/B/Power_Inlet_x1.stl

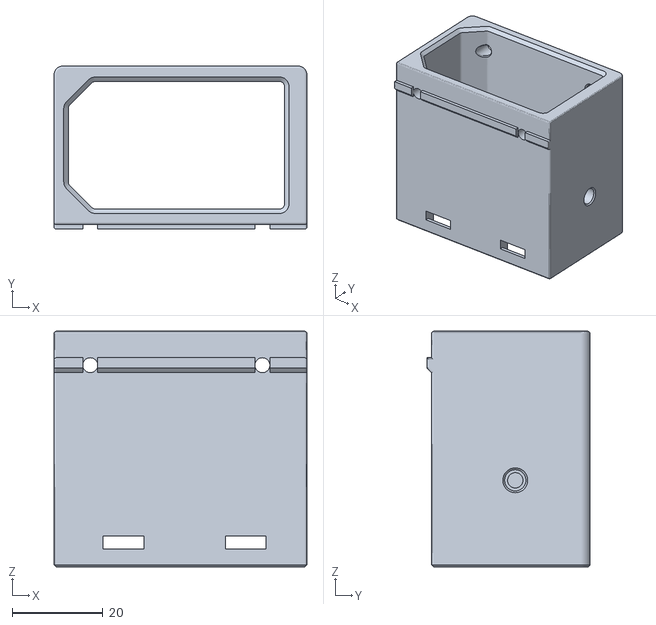
[picture p78: CAD file, 2023-02-20]
VORON Print Files/Bunged Up Files (Made for v0.1)/Regular Parts/Batch 1/B/Power_Inlet_x1.stl
55.9 x 36.0 x 52.0
