besser435/Ted/VORON Print Files/Bunged Up Files (Made for v0.1)/Regular Parts/Batch 2 (B)/(B) Batch 2.3mf

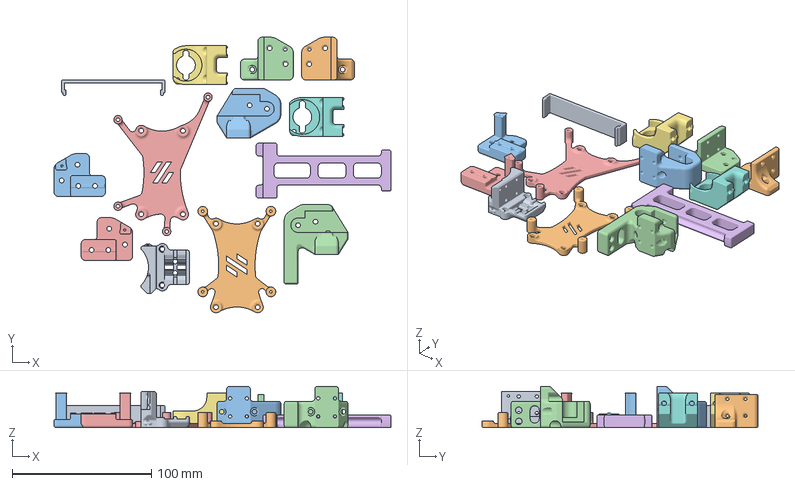
[picture p79: CAD file, 2023-02-20]
VORON Print Files/Bunged Up Files (Made for v0.1)/Regular Parts/Batch 2 (B)/(B) Batch 2.3mf
242.2 x 198.1 x 29.8 mm
PSU_Cover_x1.STL
Raspberry_Pi_3b_Mount_x1.stl
Rear_Bed_Mount_Left_x1.stl
Rear_Bed_Mount_Right_x1.stl
Skr_E3_Mounting_Bracket_x1.stl
Spool_Holder_V0_x1.STL
T8_Nut_Block_16mmx22mmOD_x1.STL
T8_Nut_Block_18mmx24mmOD_x1.STL
X_Carriage_90_x1.STL
XY_Joint_Left_Lower_x1.stl
XY_Joint_Left_Upper_x1.stl
XY_Joint_Right_Lower_x1.stl
XY_Joint_Right_Upper_x1.stl
