besser435/Ted/VORON Print Files/Bunged Up Files (Made for v0.1)/Tools/Tools.3mf

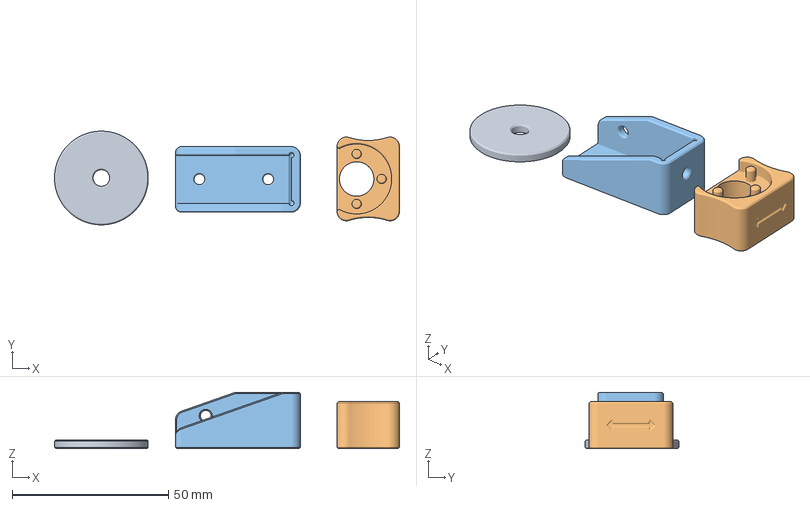
[picture p80: CAD file, 2023-02-20]
VORON Print Files/Bunged Up Files (Made for v0.1)/Tools/Tools.3mf
110.4 x 30.0 x 18.0 mm
BMG_Shaft_Mod_Spacer_x1.STL
T-Nut_Mod_Tool_x1.STL
V0_Extrusion_Drilling_Guide_x1.STL
