besser435/Ted/VORON Print Files/Bunged Up Files (Made for v0.1)/V6 Extruder/B/(B) Toolhead left, right.3mf

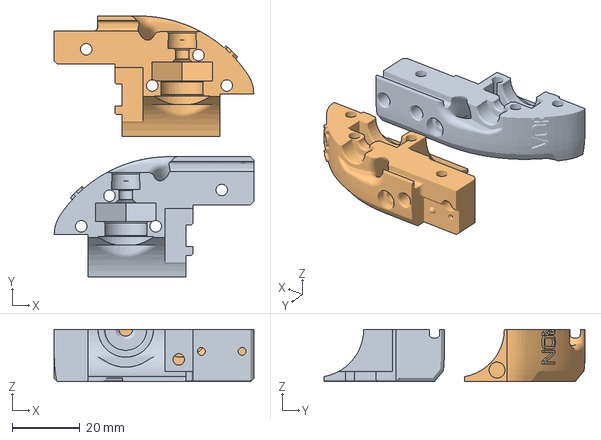
[picture p81: CAD file, 2023-02-20]
VORON Print Files/Bunged Up Files (Made for v0.1)/V6 Extruder/B/(B) Toolhead left, right.3mf
59.0 x 77.1 x 15.4 mm
Toolhead_Left_Threaded_V6_x1.STL
Toolhead_Right_Threaded_V6_x1.STL
