besser435/Ted/VORON Print Files/Bunged Up Files (Made for v0.1)/Voron-0-0.1/DXF/Motor_Panel_x1.DXF

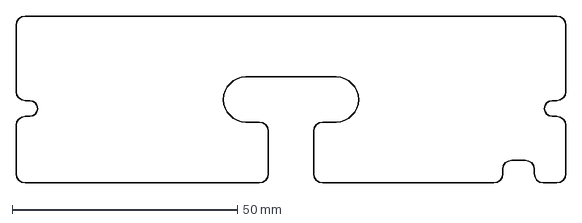
[picture p82: CAD file, 2023-02-20]
VORON Print Files/Bunged Up Files (Made for v0.1)/Voron-0-0.1/DXF/Motor_Panel_x1.DXF
122.0 x 37.0 mm
