besser435/Ted/VORON Print Files/Bunged Up Files (Made for v0.1)/Voron-0-0.1/DXF/Tophat/Top_v0.1_x1.DXF

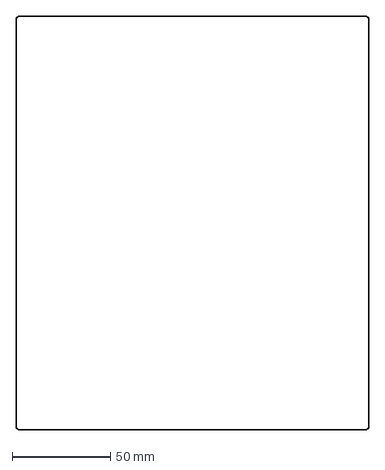
[picture p83: CAD file, 2023-02-20]
VORON Print Files/Bunged Up Files (Made for v0.1)/Voron-0-0.1/DXF/Tophat/Top_v0.1_x1.DXF
179.8 x 211.0 mm
