besser435/Ted/VORON Print Files/Bunged Up Files (Made for v0.1)/Voron-0-0.1/STLs/B_Idler_Lower_x1.stl

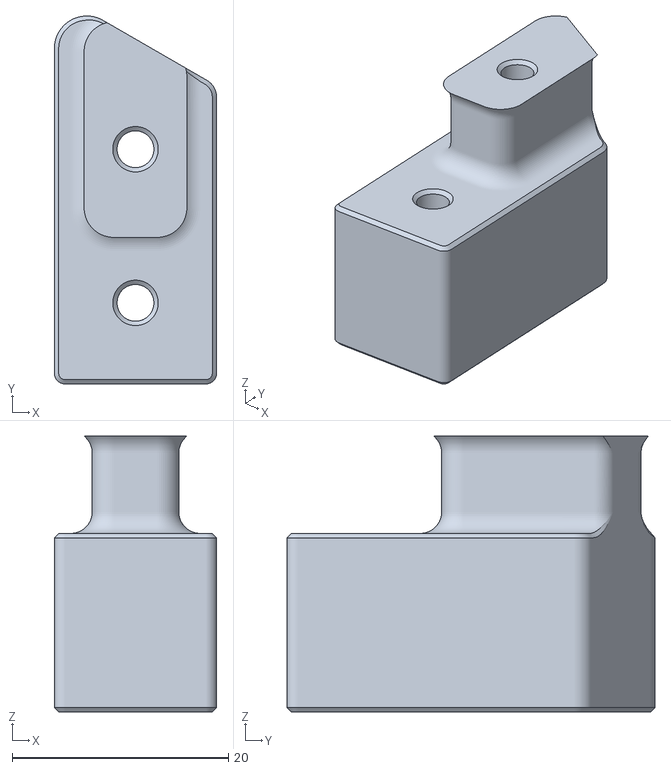
[picture p84: CAD file, 2023-02-20]
VORON Print Files/Bunged Up Files (Made for v0.1)/Voron-0-0.1/STLs/B_Idler_Lower_x1.stl
15.0 x 34.0 x 25.5
