besser435/Ted/VORON Print Files/Bunged Up Files (Made for v0.1)/Voron-0-0.1/STLs/Toolheads/Mini_Afterburner/[a]_Mid_Body_x1.stl

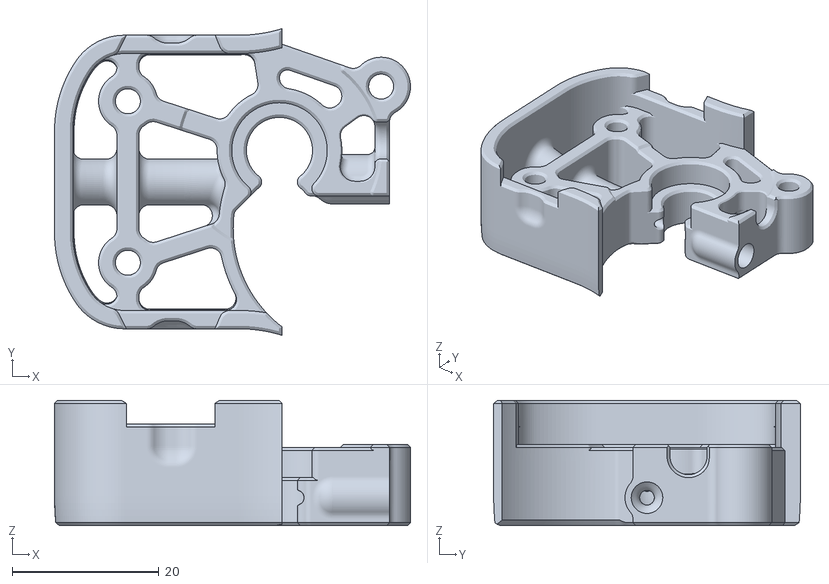
[picture p85: CAD file, 2023-02-20]
VORON Print Files/Bunged Up Files (Made for v0.1)/Voron-0-0.1/STLs/Toolheads/Mini_Afterburner/[a]_Mid_Body_x1.stl
48.5 x 41.8 x 17.0
