besser435/Ted/VORON Print Files/Enclosure/For_2.5mm_Panels/2point5mm_Middle_Clip_x9.STL

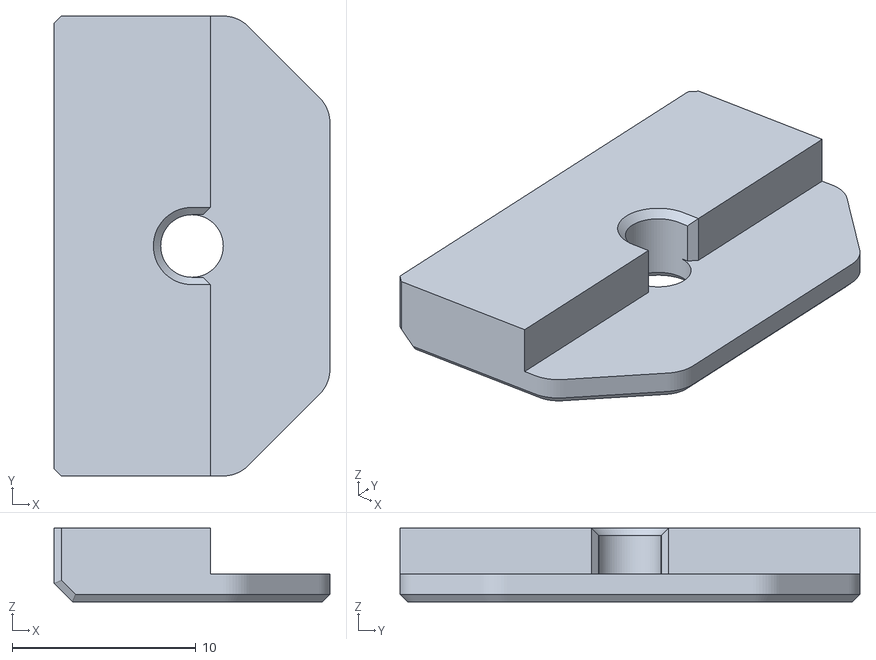
[picture p86: CAD file, 2023-02-20]
VORON Print Files/Enclosure/For_2.5mm_Panels/2point5mm_Middle_Clip_x9.STL
15.0 x 25.0 x 4.00
