besser435/Ted/VORON Print Files/Main Parts/Batch 1 Main Parts/Accent Batch 1 Main Parts/[a]_B_Drive_Tensioner_x1.STL

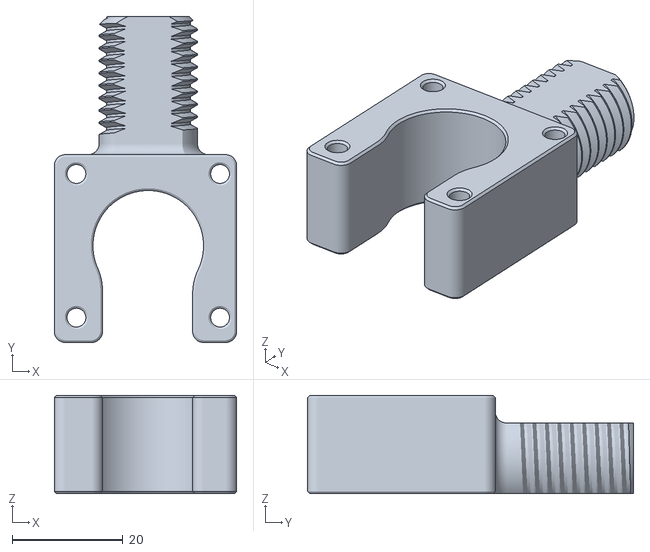
[picture p87: CAD file, 2023-02-20]
VORON Print Files/Main Parts/Batch 1 Main Parts/Accent Batch 1 Main Parts/[a]_B_Drive_Tensioner_x1.STL
33.0 x 59.0 x 17.8
