besser435/Ted/VORON Print Files/Main Parts/Multiples Main Parts/Multiple Accent Parts/Accent Multiple Parts.3mf

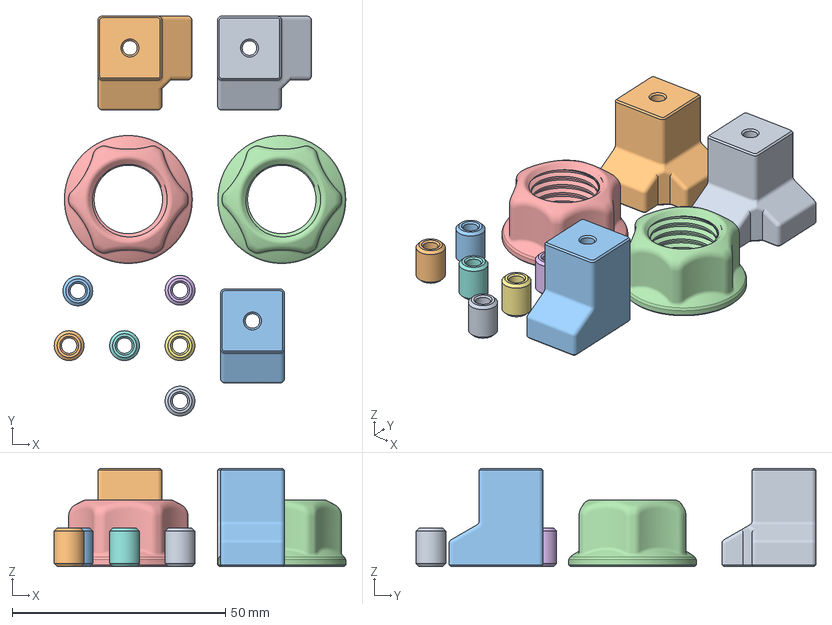
[picture p88: CAD file, 2023-02-20]
VORON Print Files/Main Parts/Multiples Main Parts/Multiple Accent Parts/Accent Multiple Parts.3mf
68.4 x 93.8 x 23.0 mm
[a]_Foot_Front_x2.stl
[a]_Foot_Rear_x2.STL
[a]_Tensioner_Knob_x2.STL
[a]_9mm_Printed_Spacer_x6.STL
