besser435/Ted/VORON Print Files/Toolhead/Accent Toolhead/Accent Toolhead.3mf

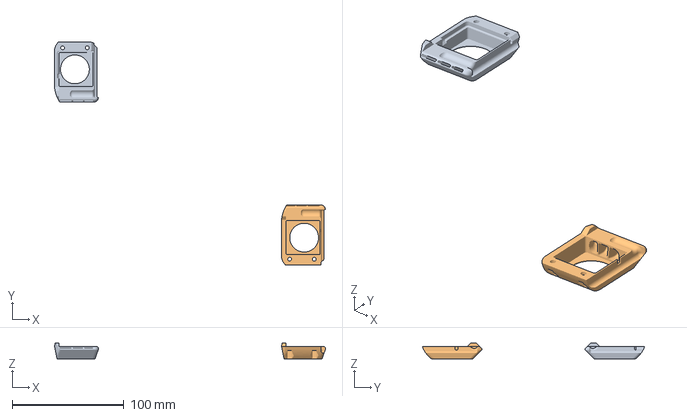
[picture p89: CAD file, 2023-02-20]
VORON Print Files/Toolhead/Accent Toolhead/Accent Toolhead.3mf
242.0 x 198.7 x 14.1 mm
[a]_Toolhead_Blower_Duct_Left_TV6_x1.STL
[a]_Toolhead_Blower_Duct_Right_TV6_x1.STL
