besser435/Ted/VORON Print Files/Toolhead/Toolhead.3mf

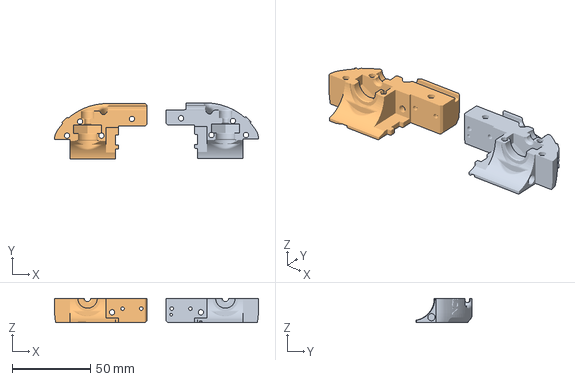
[picture p90: CAD file, 2023-02-20]
VORON Print Files/Toolhead/Toolhead.3mf
130.4 x 36.0 x 15.4 mm
Toolhead_Right_Threaded_V6_x1.STL
Toolhead_Left_Threaded_V6_x1.STL
