besser435/Ted/VORON Print Files/VORON-0 Everything/DXFs/Deck_Panel_V0.DXF

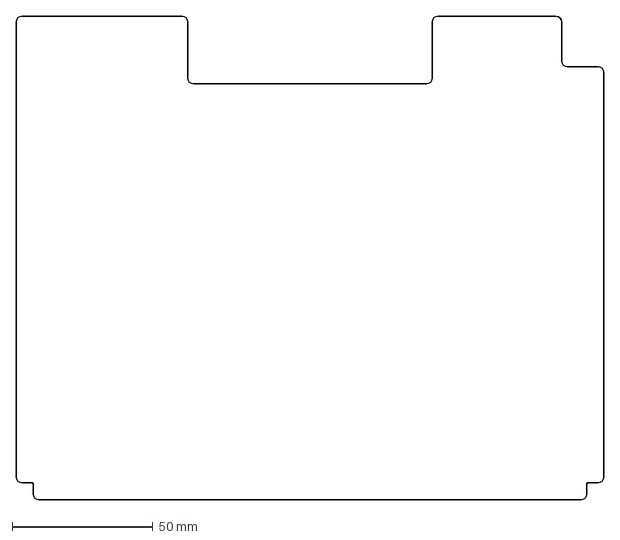
[picture p91: CAD file, 2023-02-20]
VORON Print Files/VORON-0 Everything/DXFs/Deck_Panel_V0.DXF
209.0 x 172.0 mm
