besser435/Ted/VORON Print Files/VORON-0 Everything/STLs/V0_Panel_Mounting/For_3mm_Panels/3mm_Hinge_Top_A_x1.stl

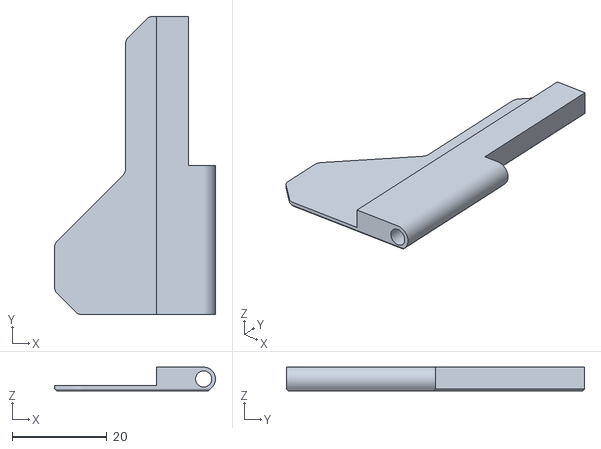
[picture p92: CAD file, 2023-02-20]
VORON Print Files/VORON-0 Everything/STLs/V0_Panel_Mounting/For_3mm_Panels/3mm_Hinge_Top_A_x1.stl
34.0 x 63.0 x 5.00
